ShakedDanZilberman/Magdad/yolo/dataset/test/images/WIN_20250122_15_49_03_Pro_jpg.rf.846b7e2bad95659f3d99197f02cc243a.jpg

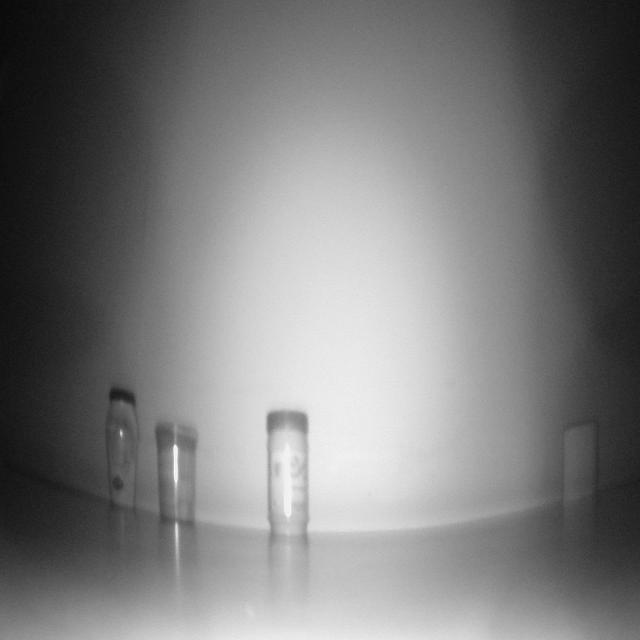
yolo/dataset/test/images/WIN_20250122_15_49_03_Pro_jpg.rf.846b7e2bad95659f3d99197f02cc243a.jpg
