ShakedDanZilberman/Magdad/camera-training-1/valid/images/Screenshot-2025-01-09-204010_jpg.rf.81b5915cf226393bbc3c557325b8a174.jpg

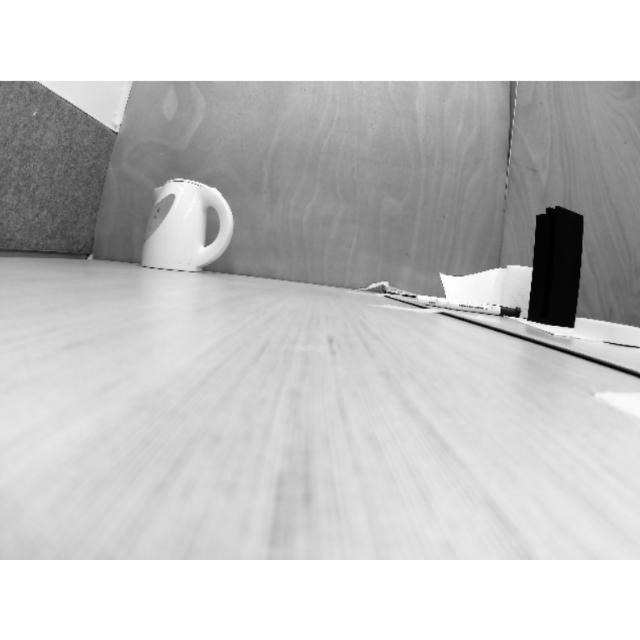
camera-training-1/valid/images/Screenshot-2025-01-09-204010_jpg.rf.81b5915cf226393bbc3c557325b8a174.jpg
