ShakedDanZilberman/Magdad/camera-training-1/valid/images/Screenshot-2025-01-09-204149_jpg.rf.caab2a580253b0b938889a33d17098a2.jpg

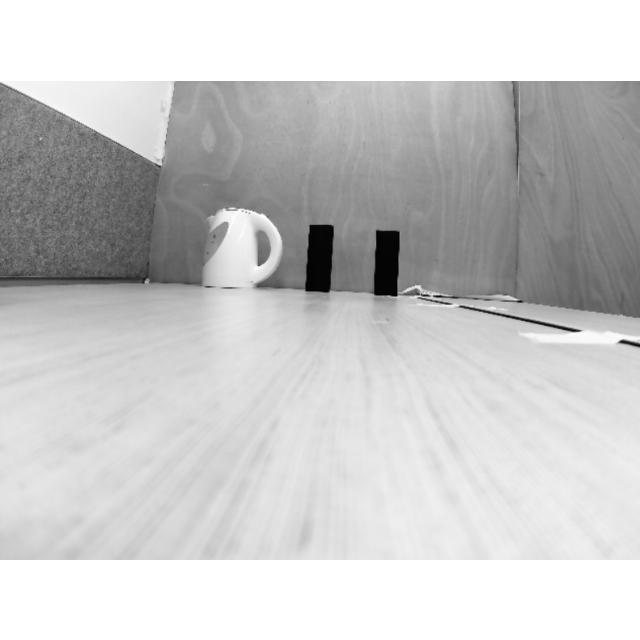
camera-training-1/valid/images/Screenshot-2025-01-09-204149_jpg.rf.caab2a580253b0b938889a33d17098a2.jpg
