ShakedDanZilberman/Magdad/camera-training-1/valid/images/Screenshot-2025-01-09-204222_jpg.rf.880aa902dc17edb48ca99602dae9c156.jpg

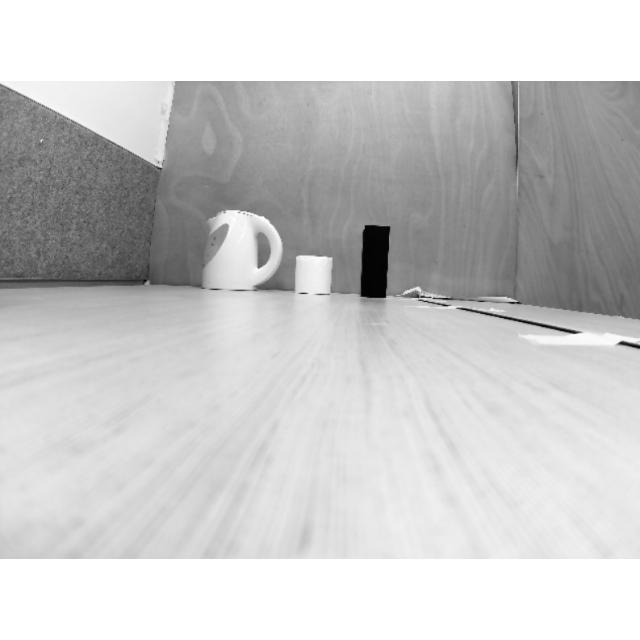
camera-training-1/valid/images/Screenshot-2025-01-09-204222_jpg.rf.880aa902dc17edb48ca99602dae9c156.jpg
