ShakedDanZilberman/Magdad/camera-training-1/valid/images/Screenshot-2025-01-09-204408_jpg.rf.71805534d5d2c8054f3e4067cf0431f8.jpg

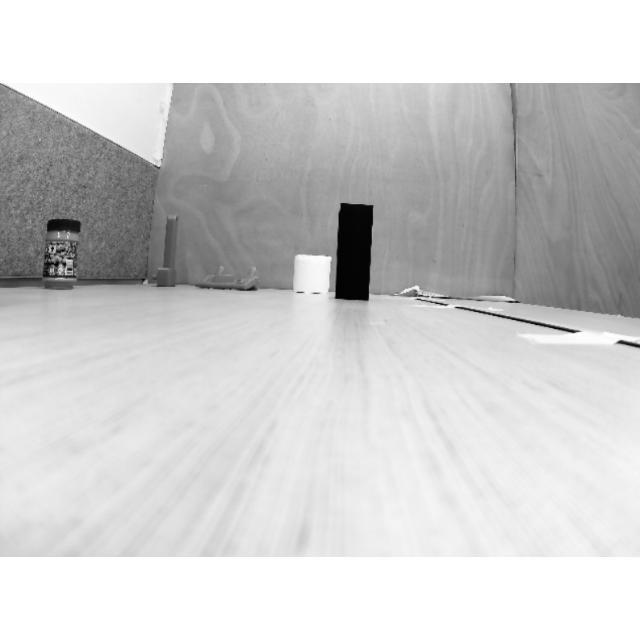
camera-training-1/valid/images/Screenshot-2025-01-09-204408_jpg.rf.71805534d5d2c8054f3e4067cf0431f8.jpg
