ShakedDanZilberman/Magdad/camera-training-1/valid/images/Screenshot-2025-01-09-204434_jpg.rf.ee736907abe9e383c5cfcaa76f32814a.jpg

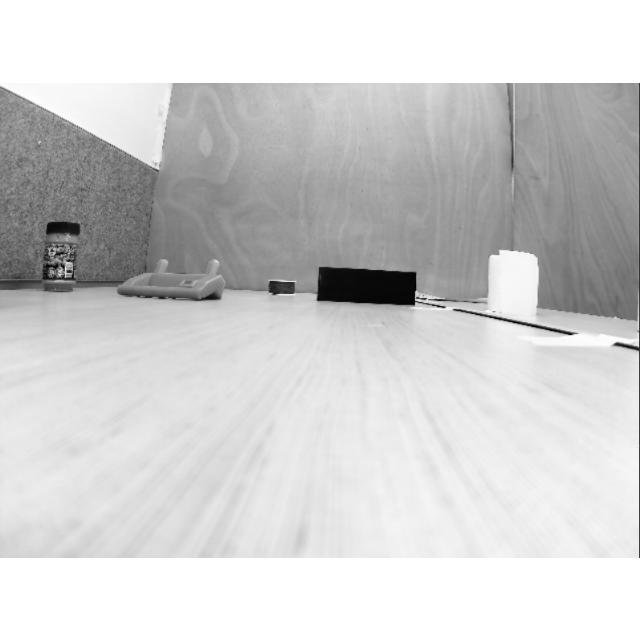
camera-training-1/valid/images/Screenshot-2025-01-09-204434_jpg.rf.ee736907abe9e383c5cfcaa76f32814a.jpg
