ShakedDanZilberman/Magdad/camera-training-1/valid/images/Screenshot-2025-01-09-204518_jpg.rf.a492691f899624e1c3656ebf20315830.jpg

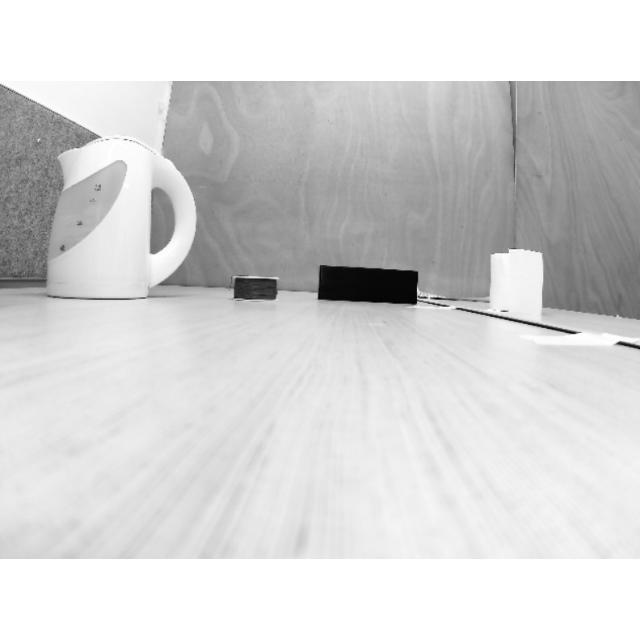
camera-training-1/valid/images/Screenshot-2025-01-09-204518_jpg.rf.a492691f899624e1c3656ebf20315830.jpg
