ShakedDanZilberman/Magdad/camera-training-2/train/images/WIN_20250113_22_33_18_Pro_jpg.rf.e2d5ad69d18867120f0af434011adf48.jpg

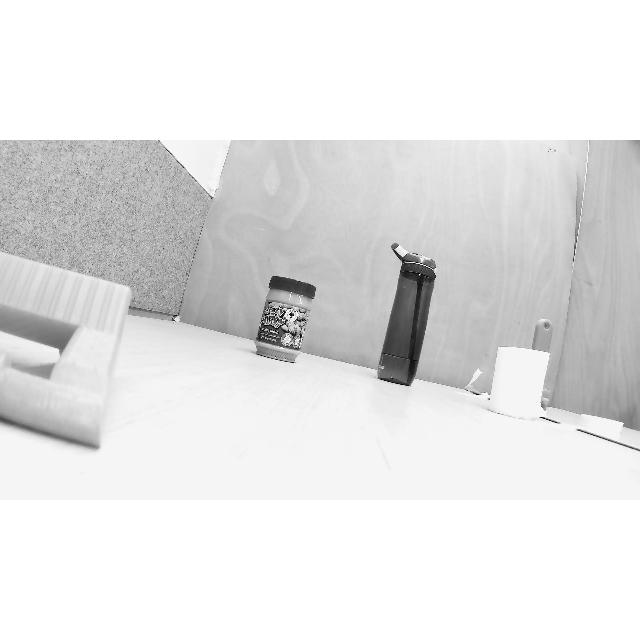
camera-training-2/train/images/WIN_20250113_22_33_18_Pro_jpg.rf.e2d5ad69d18867120f0af434011adf48.jpg
