ShakedDanZilberman/Magdad/camera-training-2/train/images/WIN_20250113_22_33_43_Pro_jpg.rf.7a9c28b805c44db4745cd09ba6515cde.jpg

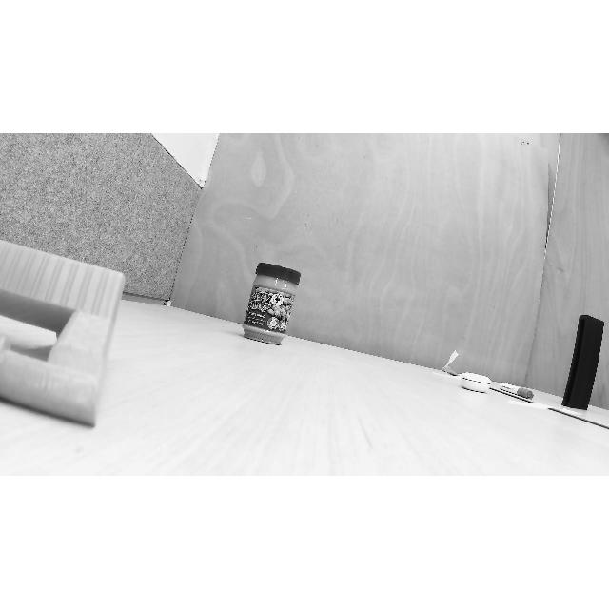
camera-training-2/train/images/WIN_20250113_22_33_43_Pro_jpg.rf.7a9c28b805c44db4745cd09ba6515cde.jpg
