ShakedDanZilberman/Magdad/camera-training-2/train/images/WIN_20250113_22_34_02_Pro_jpg.rf.783c1f57d91c2b72b632802cee9630df.jpg

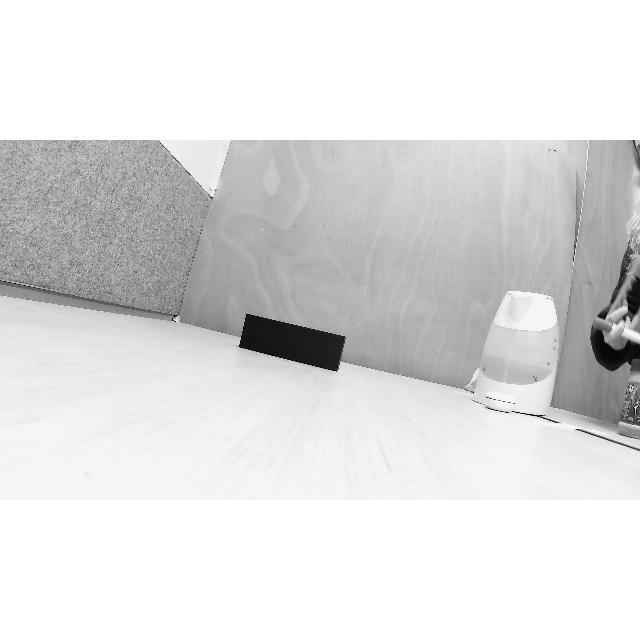
camera-training-2/train/images/WIN_20250113_22_34_02_Pro_jpg.rf.783c1f57d91c2b72b632802cee9630df.jpg
