ShakedDanZilberman/Magdad/camera-training-2/train/images/WIN_20250113_22_34_42_Pro_jpg.rf.ab0f6944b360db3d50f486841ce7cbbd.jpg

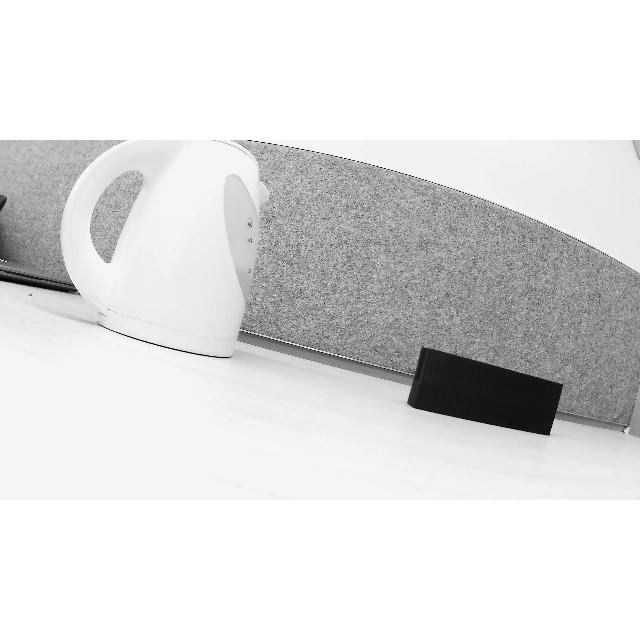
camera-training-2/train/images/WIN_20250113_22_34_42_Pro_jpg.rf.ab0f6944b360db3d50f486841ce7cbbd.jpg
