ShakedDanZilberman/Magdad/camera-training-2/train/images/WIN_20250113_22_34_53_Pro_jpg.rf.5d67e8cbfae78bd698f9c18f5c3b9999.jpg

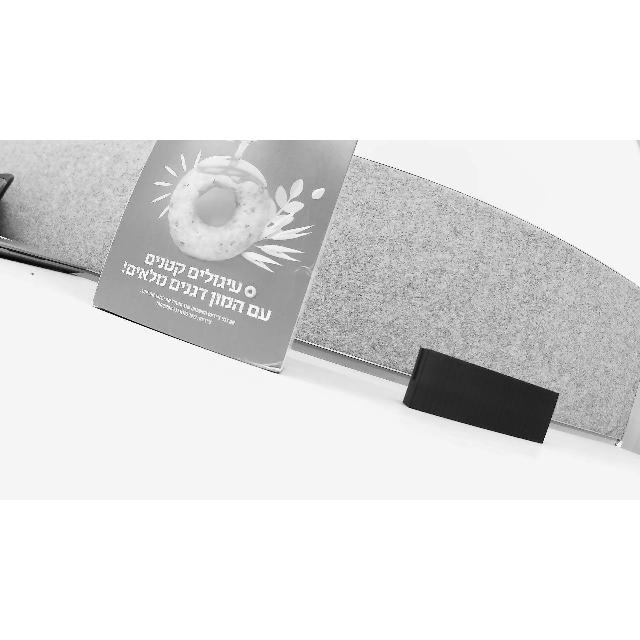
camera-training-2/train/images/WIN_20250113_22_34_53_Pro_jpg.rf.5d67e8cbfae78bd698f9c18f5c3b9999.jpg
