ShakedDanZilberman/Magdad/camera-training-2/train/images/WIN_20250113_22_35_08_Pro_jpg.rf.ca820dc60fe7edaa0e6810bf6f3705b2.jpg

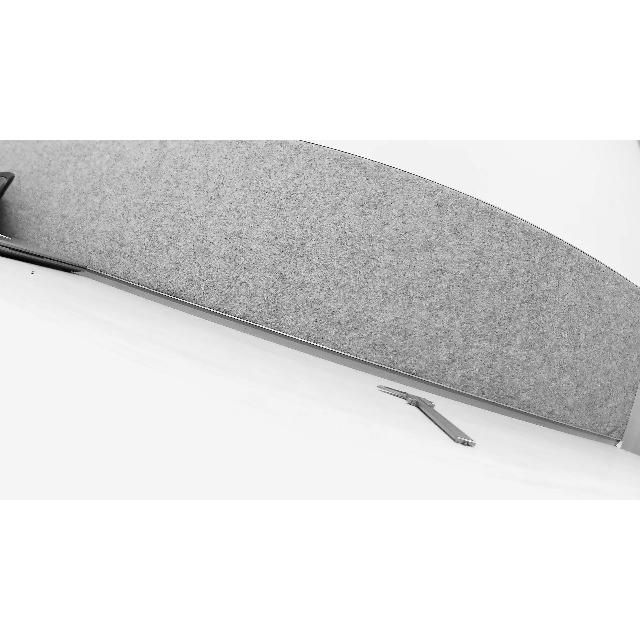
camera-training-2/train/images/WIN_20250113_22_35_08_Pro_jpg.rf.ca820dc60fe7edaa0e6810bf6f3705b2.jpg
