ShakedDanZilberman/Magdad/camera-training-2/train/images/WIN_20250113_22_35_11_Pro_jpg.rf.4013db7eb432c82a8826c612f844e487.jpg

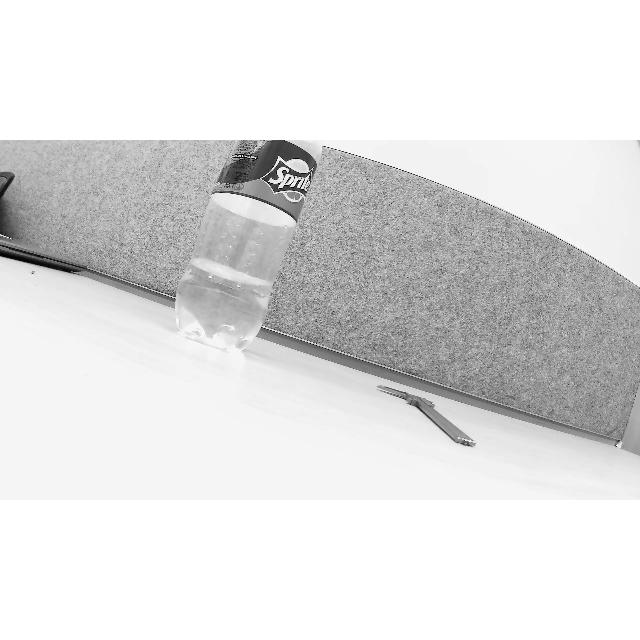
camera-training-2/train/images/WIN_20250113_22_35_11_Pro_jpg.rf.4013db7eb432c82a8826c612f844e487.jpg
