ShakedDanZilberman/Magdad/camera-training-2/train/images/WIN_20250113_22_35_16_Pro_jpg.rf.52b17507b7d4b6b88c684b167f2d8827.jpg

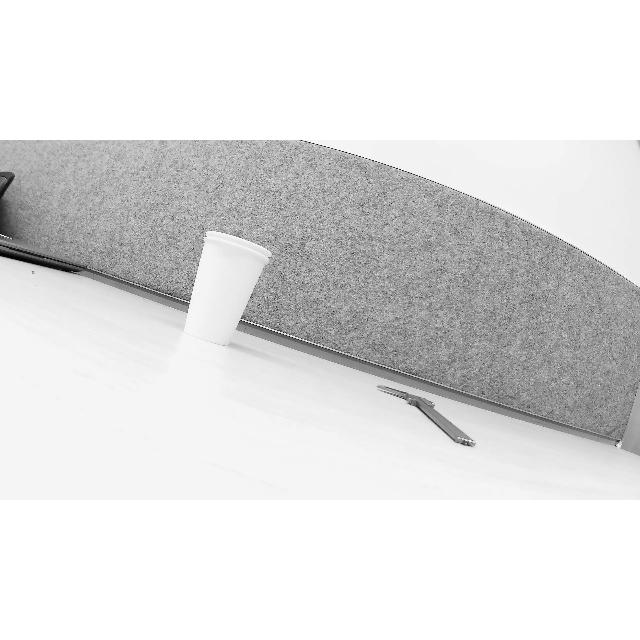
camera-training-2/train/images/WIN_20250113_22_35_16_Pro_jpg.rf.52b17507b7d4b6b88c684b167f2d8827.jpg
