ShakedDanZilberman/Magdad/camera-training-2/train/images/WIN_20250113_22_35_22_Pro_jpg.rf.d8e230dd37e21a51529a2eac11b03157.jpg

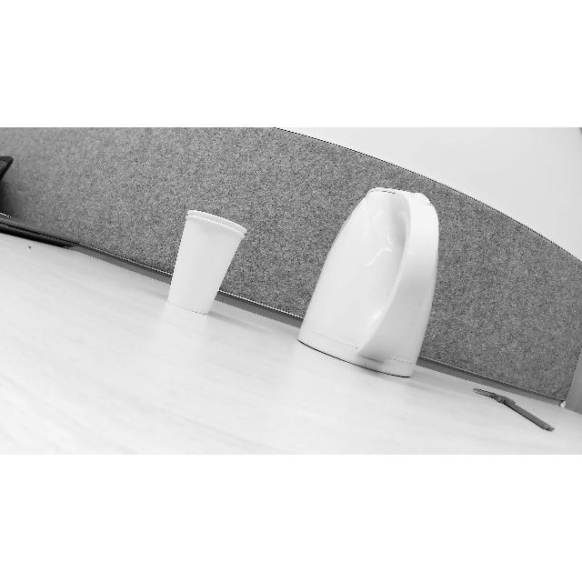
camera-training-2/train/images/WIN_20250113_22_35_22_Pro_jpg.rf.d8e230dd37e21a51529a2eac11b03157.jpg
