ShakedDanZilberman/Magdad/camera-training-2/train/images/WIN_20250113_22_36_17_Pro_jpg.rf.434e08e763b4095fee1812178f245678.jpg

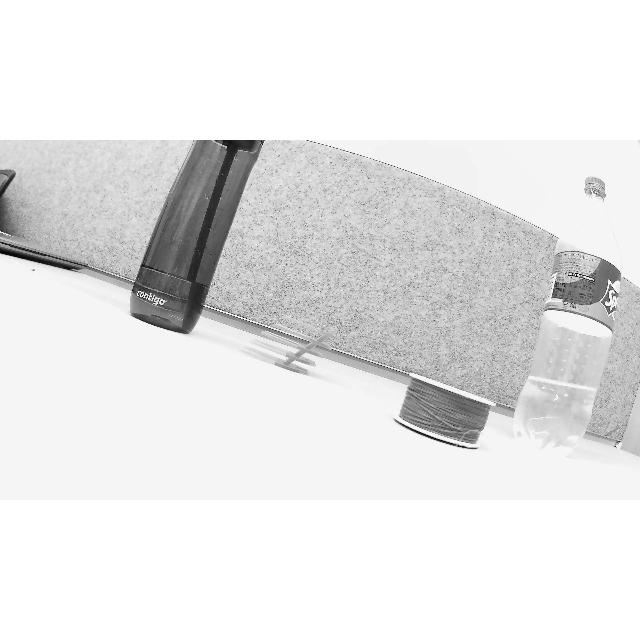
camera-training-2/train/images/WIN_20250113_22_36_17_Pro_jpg.rf.434e08e763b4095fee1812178f245678.jpg
