ShakedDanZilberman/Magdad/camera-training-2/train/images/WIN_20250113_22_37_04_Pro_jpg.rf.e61e84cb694f8d44666576b0f4bd507f.jpg

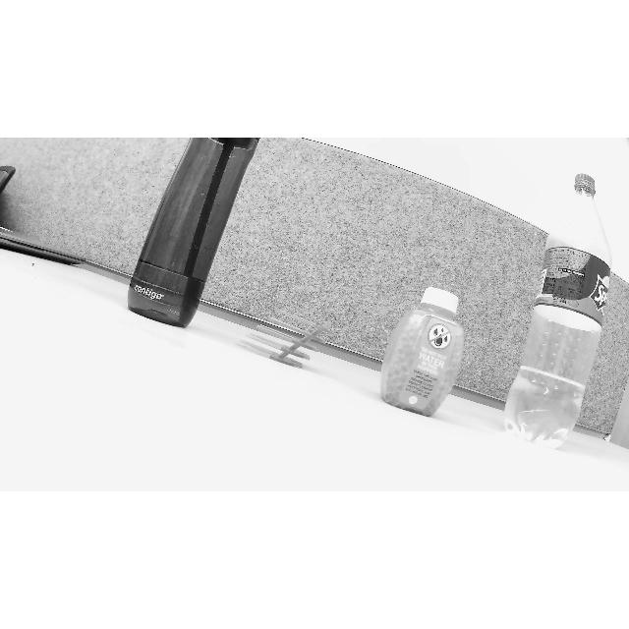
camera-training-2/train/images/WIN_20250113_22_37_04_Pro_jpg.rf.e61e84cb694f8d44666576b0f4bd507f.jpg
