ShakedDanZilberman/Magdad/camera-training-2/train/images/WIN_20250113_22_37_08_Pro_jpg.rf.a589353bd3baeb06a9639a7202b36bbc.jpg

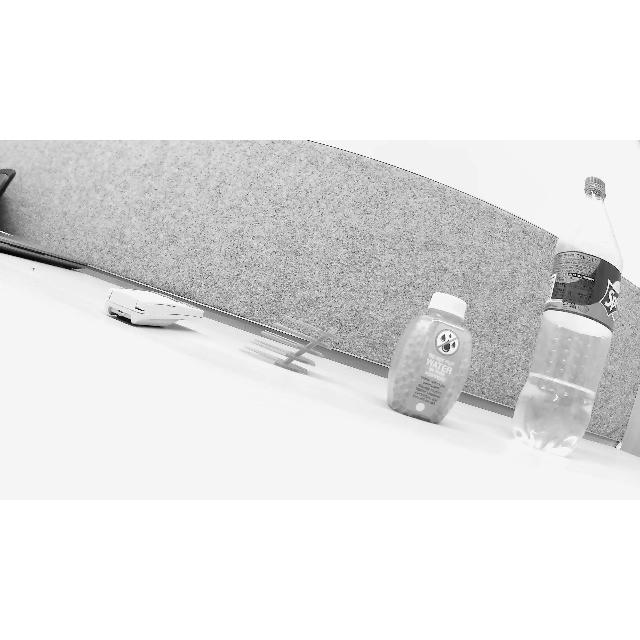
camera-training-2/train/images/WIN_20250113_22_37_08_Pro_jpg.rf.a589353bd3baeb06a9639a7202b36bbc.jpg
