ShakedDanZilberman/Magdad/camera-training-2/train/images/WIN_20250113_22_37_36_Pro_jpg.rf.b33690e6ef2aee6fb451731b02019a81.jpg

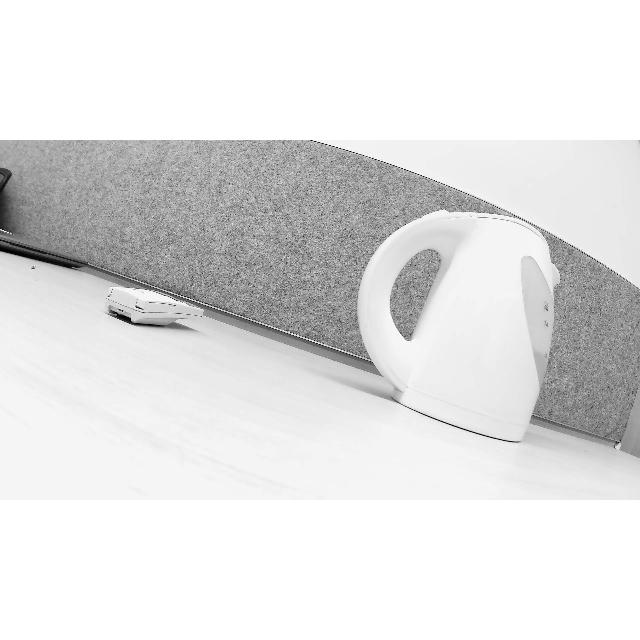
camera-training-2/train/images/WIN_20250113_22_37_36_Pro_jpg.rf.b33690e6ef2aee6fb451731b02019a81.jpg
