ShakedDanZilberman/Magdad/camera-training-2/train/images/WIN_20250113_22_37_51_Pro_jpg.rf.b9c5b7d6a7c29c52d90a4989442c4607.jpg

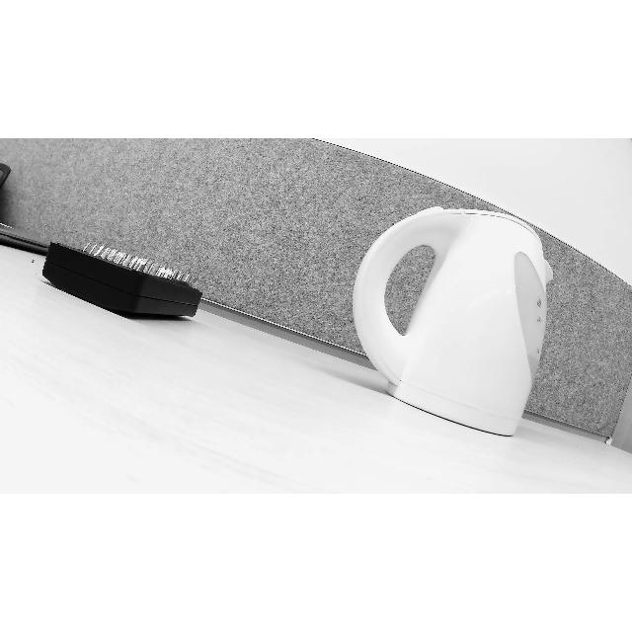
camera-training-2/train/images/WIN_20250113_22_37_51_Pro_jpg.rf.b9c5b7d6a7c29c52d90a4989442c4607.jpg
