ShakedDanZilberman/Magdad/camera-training-2/train/images/WIN_20250113_22_38_17_Pro_jpg.rf.8e4c9293f9f154b4c6c96e188bc1d038.jpg

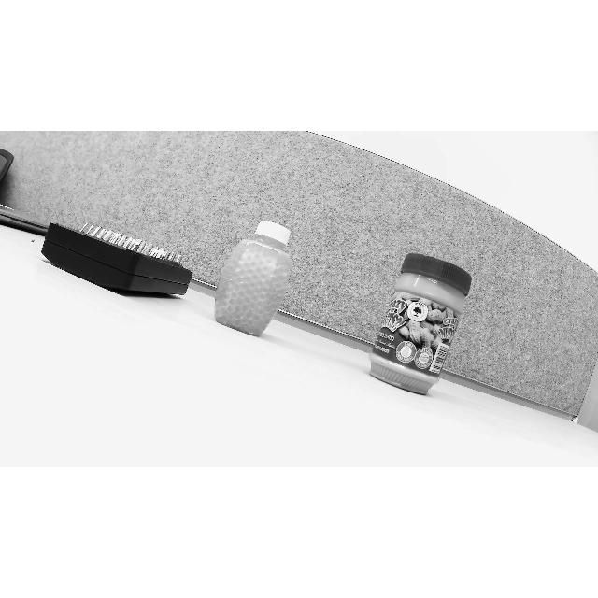
camera-training-2/train/images/WIN_20250113_22_38_17_Pro_jpg.rf.8e4c9293f9f154b4c6c96e188bc1d038.jpg
