ShakedDanZilberman/Magdad/camera-training-2/train/images/WIN_20250113_22_38_23_Pro_jpg.rf.5dbb93d275ae0dcbff493e2a2543c315.jpg

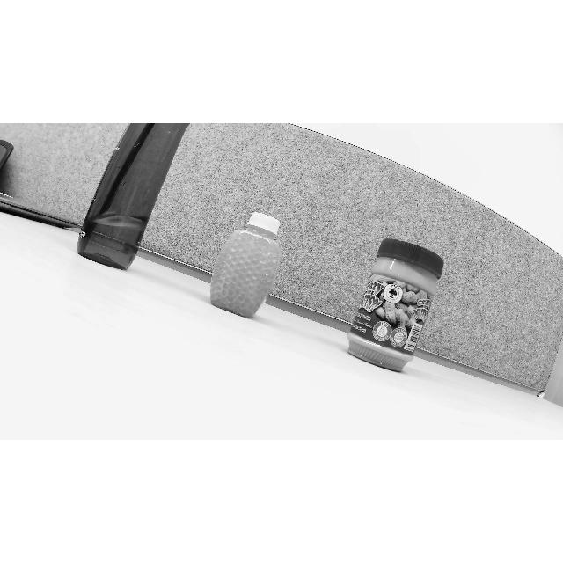
camera-training-2/train/images/WIN_20250113_22_38_23_Pro_jpg.rf.5dbb93d275ae0dcbff493e2a2543c315.jpg
