ShakedDanZilberman/Magdad/camera-training-2/train/images/WIN_20250113_22_38_47_Pro_jpg.rf.66622b3fdd767c53d6206cc575598a07.jpg

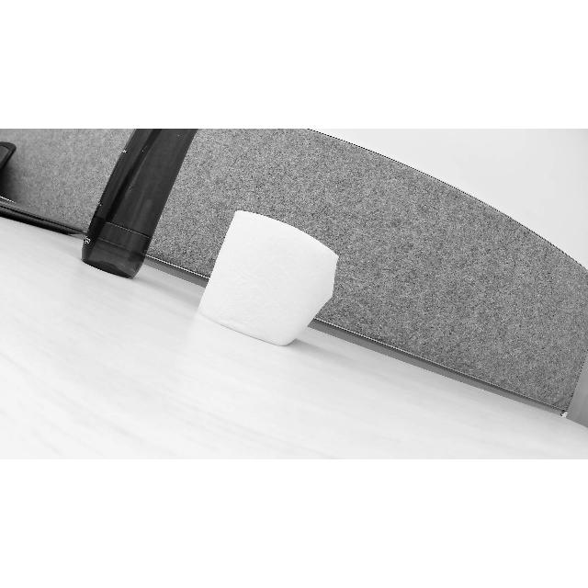
camera-training-2/train/images/WIN_20250113_22_38_47_Pro_jpg.rf.66622b3fdd767c53d6206cc575598a07.jpg
