ShakedDanZilberman/Magdad/camera-training-2/train/images/WIN_20250113_22_39_10_Pro_jpg.rf.253a86497d2ba91eef1dbaa0058f9085.jpg

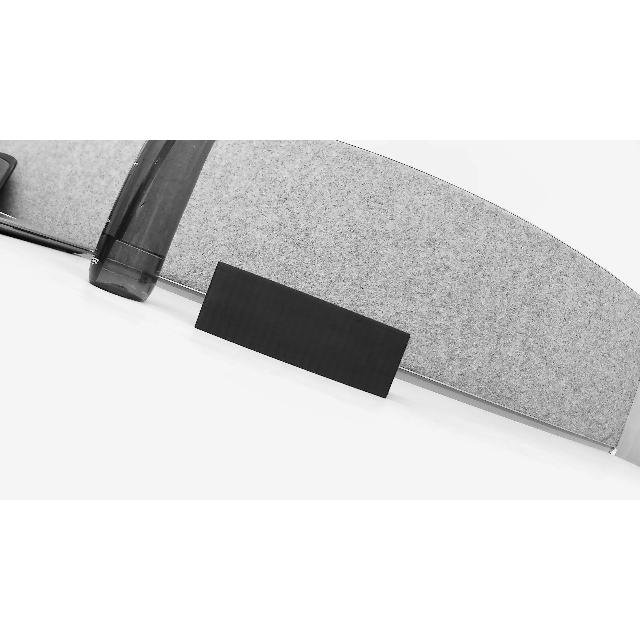
camera-training-2/train/images/WIN_20250113_22_39_10_Pro_jpg.rf.253a86497d2ba91eef1dbaa0058f9085.jpg
