ShakedDanZilberman/Magdad/camera-training-2/train/images/WIN_20250113_22_39_30_Pro_jpg.rf.a8221e1a47ee683b0f74e122a8c80f67.jpg

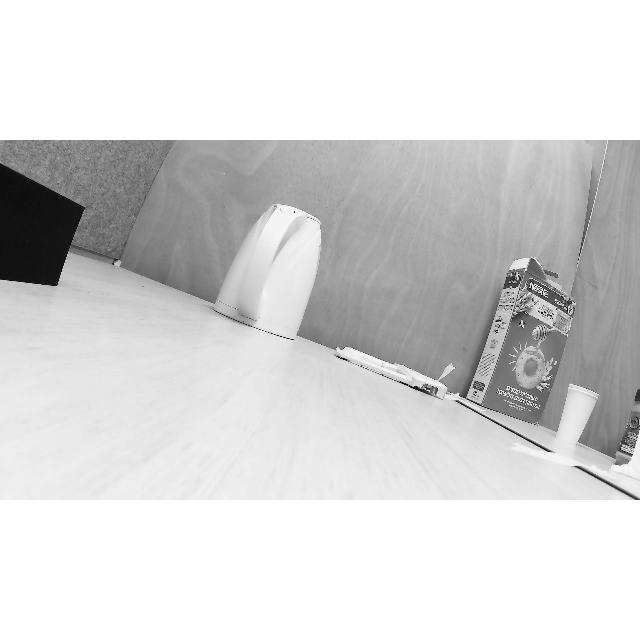
camera-training-2/train/images/WIN_20250113_22_39_30_Pro_jpg.rf.a8221e1a47ee683b0f74e122a8c80f67.jpg
