ShakedDanZilberman/Magdad/camera-training-2/train/images/WIN_20250113_22_39_38_Pro_jpg.rf.3bc607d0f519e104844494635457f564.jpg

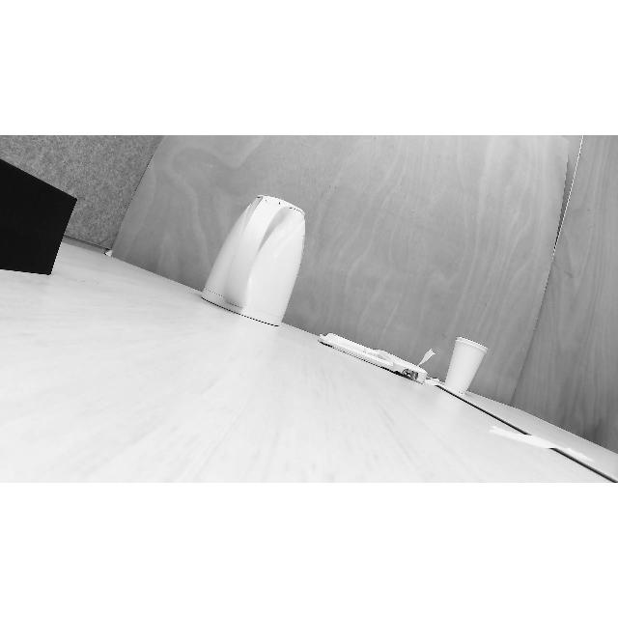
camera-training-2/train/images/WIN_20250113_22_39_38_Pro_jpg.rf.3bc607d0f519e104844494635457f564.jpg
