ShakedDanZilberman/Magdad/camera-training-2/train/images/WIN_20250113_22_40_06_Pro_jpg.rf.6f355db6460bb0738abd5323291e1bff.jpg

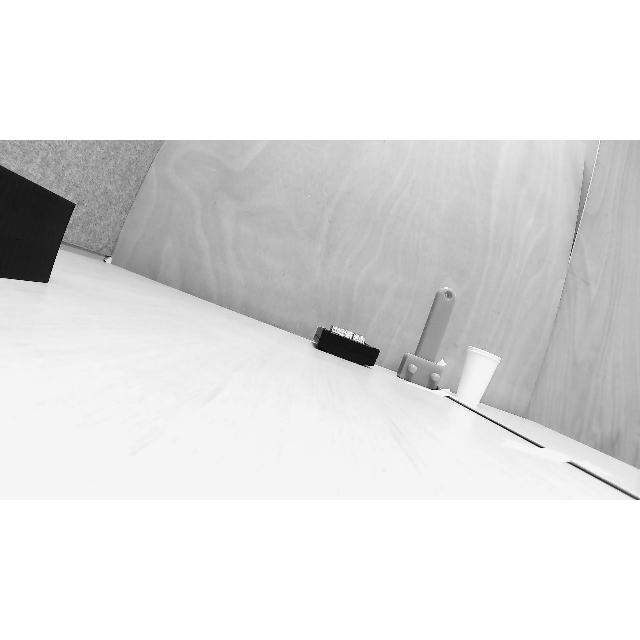
camera-training-2/train/images/WIN_20250113_22_40_06_Pro_jpg.rf.6f355db6460bb0738abd5323291e1bff.jpg
