ShakedDanZilberman/Magdad/camera-training-2/train/images/WIN_20250113_22_40_22_Pro_jpg.rf.743f60de3c918ec63ab65db9a79bd959.jpg

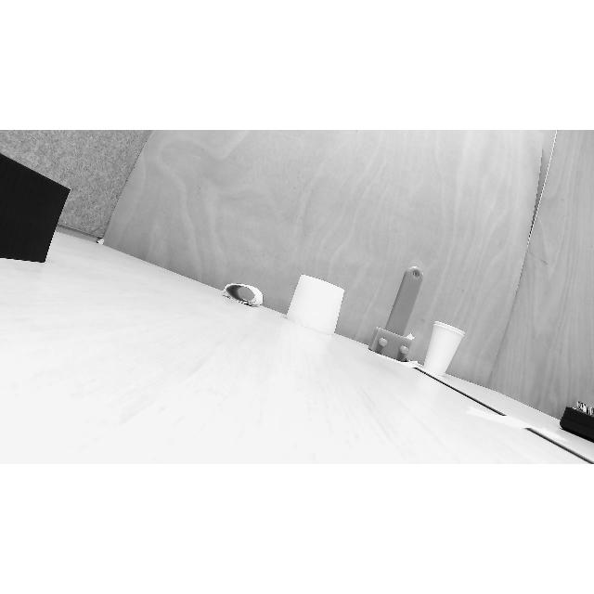
camera-training-2/train/images/WIN_20250113_22_40_22_Pro_jpg.rf.743f60de3c918ec63ab65db9a79bd959.jpg
