ShakedDanZilberman/Magdad/camera-training-2/train/images/WIN_20250113_22_41_05_Pro_jpg.rf.81757d52d88d5fbfa62f40eb433f8090.jpg

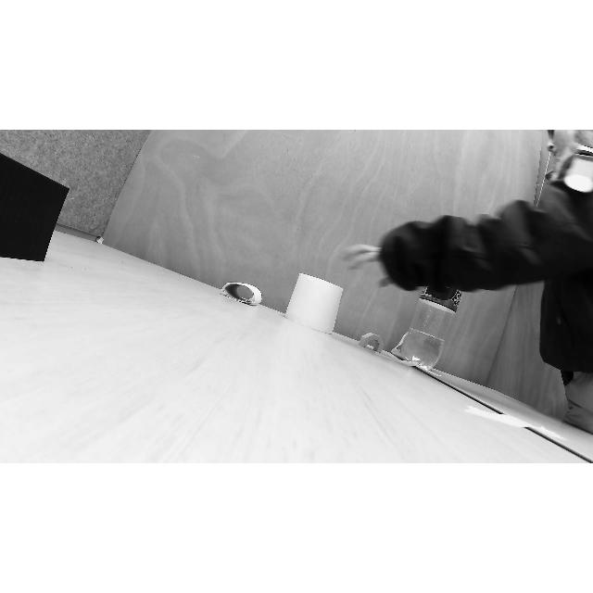
camera-training-2/train/images/WIN_20250113_22_41_05_Pro_jpg.rf.81757d52d88d5fbfa62f40eb433f8090.jpg
