ShakedDanZilberman/Magdad/camera-training-2/train/images/WIN_20250113_22_42_10_Pro_jpg.rf.32e12ff022c67c932389b7111940035a.jpg

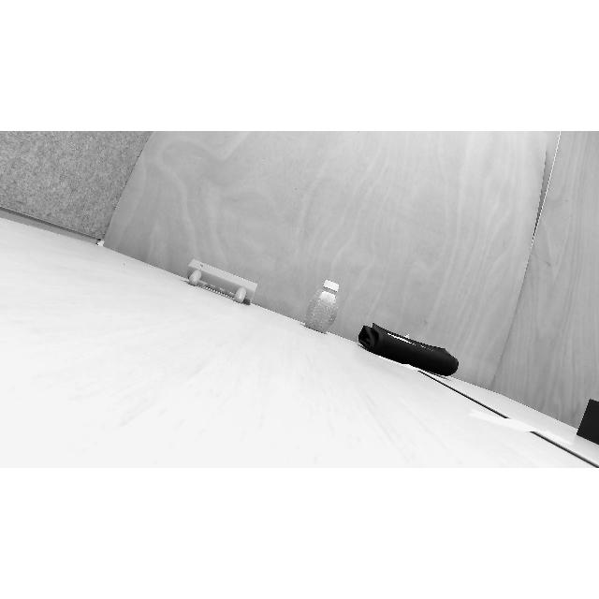
camera-training-2/train/images/WIN_20250113_22_42_10_Pro_jpg.rf.32e12ff022c67c932389b7111940035a.jpg
