ShakedDanZilberman/Magdad/camera-training-2/train/images/WIN_20250113_22_42_40_Pro_jpg.rf.92384597ecd3b0a4bffcabb38320616e.jpg

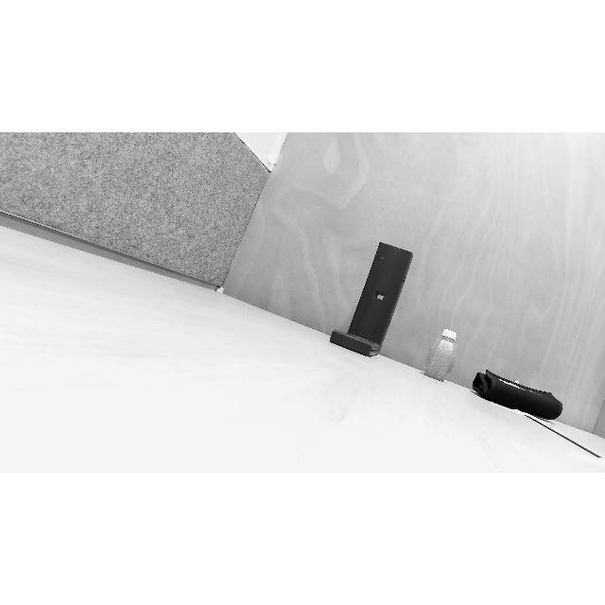
camera-training-2/train/images/WIN_20250113_22_42_40_Pro_jpg.rf.92384597ecd3b0a4bffcabb38320616e.jpg
