ShakedDanZilberman/Magdad/camera-training-2/train/images/WIN_20250113_22_42_48_Pro_jpg.rf.e93ffbc472efff108b7a3c59b1170274.jpg

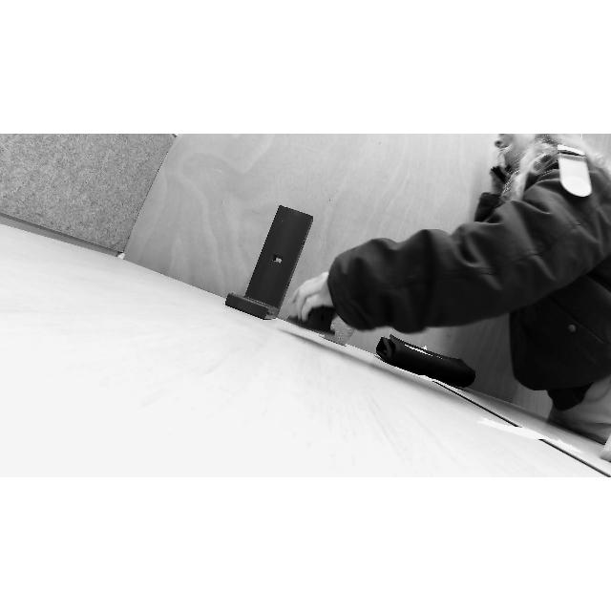
camera-training-2/train/images/WIN_20250113_22_42_48_Pro_jpg.rf.e93ffbc472efff108b7a3c59b1170274.jpg
