ShakedDanZilberman/Magdad/camera-training-2/train/images/WIN_20250113_22_43_01_Pro_jpg.rf.85477816b50bfda8253a108ba01e3208.jpg

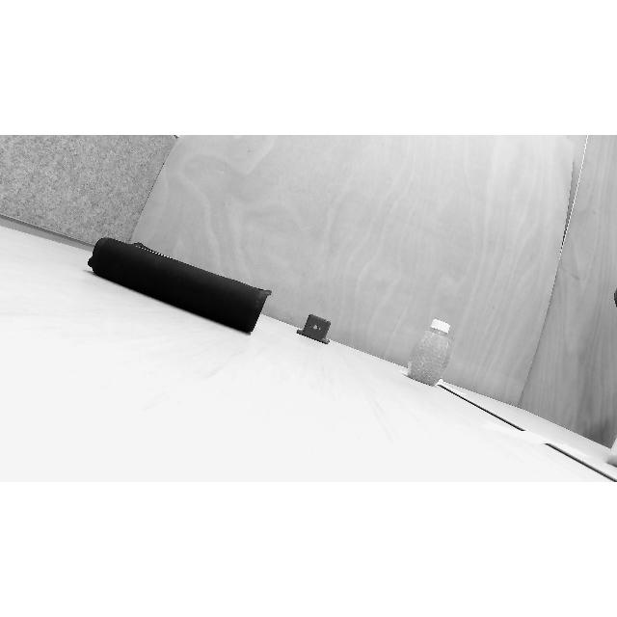
camera-training-2/train/images/WIN_20250113_22_43_01_Pro_jpg.rf.85477816b50bfda8253a108ba01e3208.jpg
