ShakedDanZilberman/Magdad/camera-training-2/train/images/WIN_20250113_22_43_12_Pro_jpg.rf.de70a53ec0a42eb00e3af8e9a14324cf.jpg

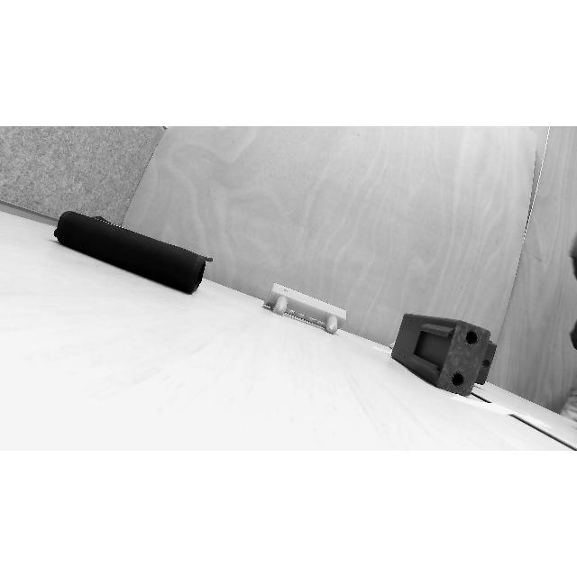
camera-training-2/train/images/WIN_20250113_22_43_12_Pro_jpg.rf.de70a53ec0a42eb00e3af8e9a14324cf.jpg
