ShakedDanZilberman/Magdad/camera-training-2/train/images/WIN_20250113_22_43_33_Pro_jpg.rf.30e844897ff9256df4f26eb0bfbda52d.jpg

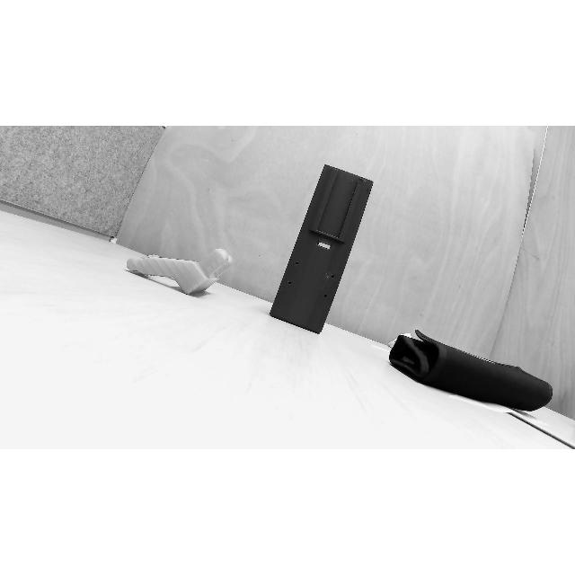
camera-training-2/train/images/WIN_20250113_22_43_33_Pro_jpg.rf.30e844897ff9256df4f26eb0bfbda52d.jpg
