ShakedDanZilberman/Magdad/camera-training-2/train/images/WIN_20250113_22_44_00_Pro_jpg.rf.20149d039af8cff58ac0f18044d618da.jpg

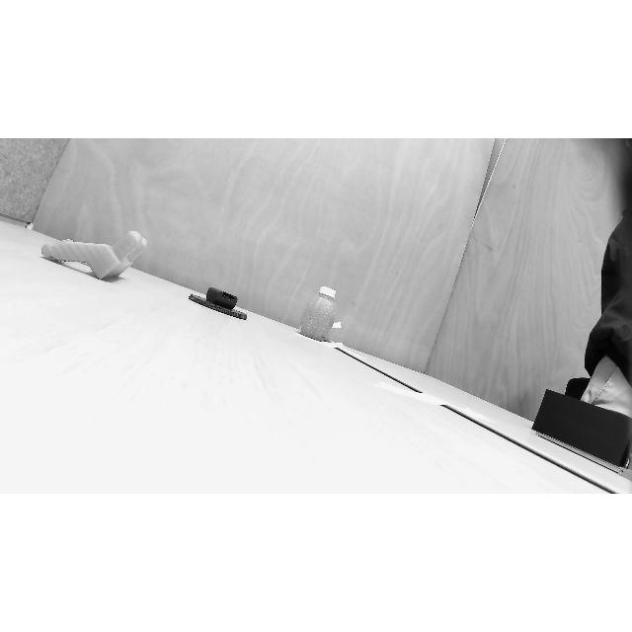
camera-training-2/train/images/WIN_20250113_22_44_00_Pro_jpg.rf.20149d039af8cff58ac0f18044d618da.jpg
