ShakedDanZilberman/Magdad/camera-training-2/train/images/WIN_20250113_22_44_12_Pro_jpg.rf.9b10c28fe63c1ae49be889de22b8d8f4.jpg

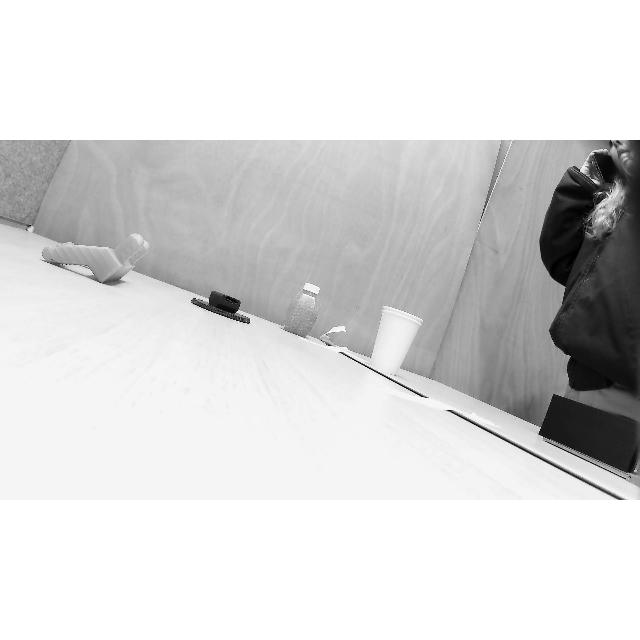
camera-training-2/train/images/WIN_20250113_22_44_12_Pro_jpg.rf.9b10c28fe63c1ae49be889de22b8d8f4.jpg
