ShakedDanZilberman/Magdad/camera-training-2/train/images/WIN_20250113_22_44_56_Pro_jpg.rf.4f9d95a4c188d3bfc7a40898143e7159.jpg

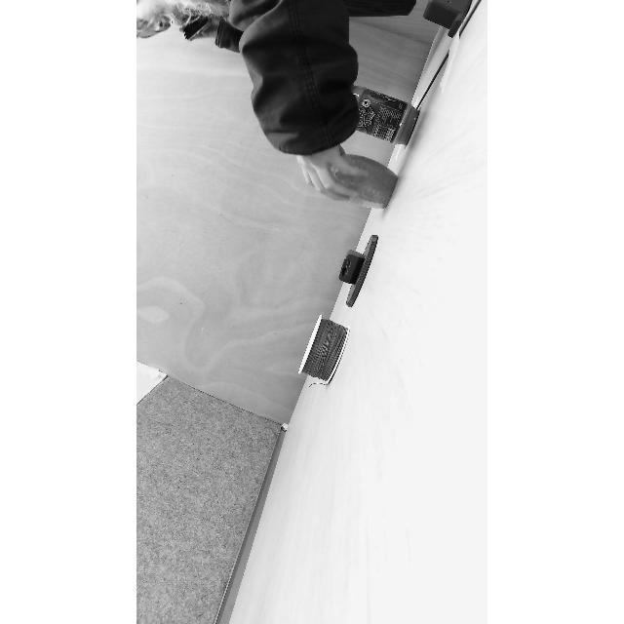
camera-training-2/train/images/WIN_20250113_22_44_56_Pro_jpg.rf.4f9d95a4c188d3bfc7a40898143e7159.jpg
