ShakedDanZilberman/Magdad/camera-training-2/train/images/WIN_20250113_22_44_57_Pro_jpg.rf.8f4678745a50cfe26ac4a26389f38c47.jpg

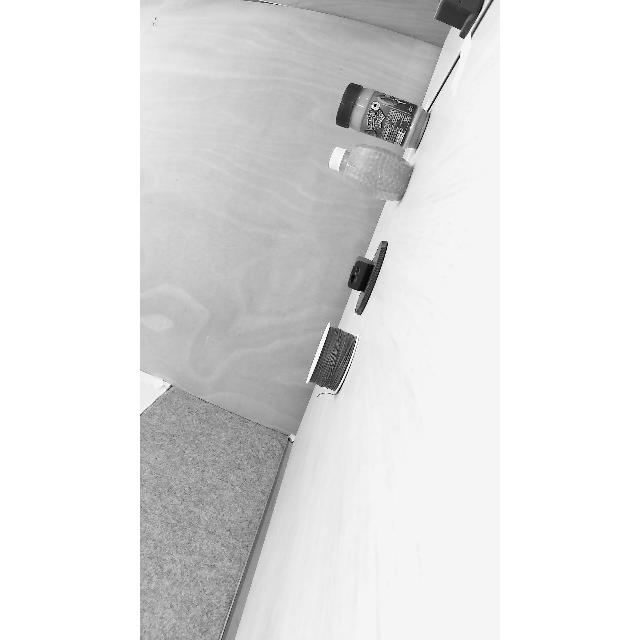
camera-training-2/train/images/WIN_20250113_22_44_57_Pro_jpg.rf.8f4678745a50cfe26ac4a26389f38c47.jpg
