ShakedDanZilberman/Magdad/camera-training-2/train/images/WIN_20250113_22_45_20_Pro_jpg.rf.0e5be70096149867ba9fe1c749a1d6bc.jpg

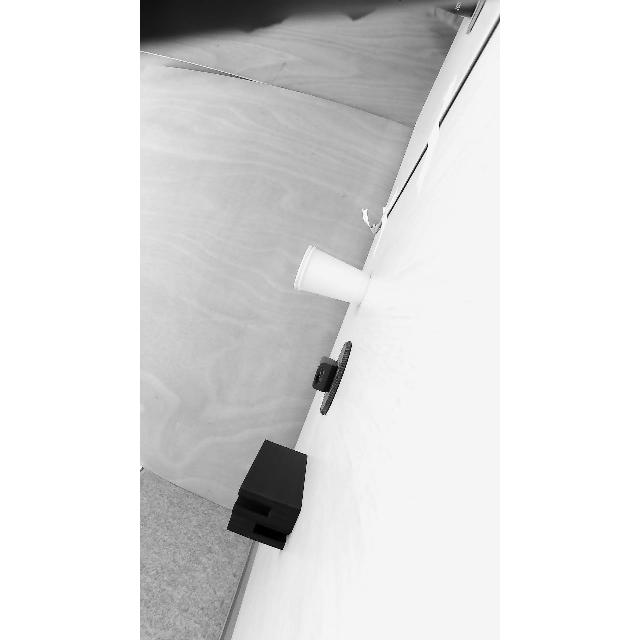
camera-training-2/train/images/WIN_20250113_22_45_20_Pro_jpg.rf.0e5be70096149867ba9fe1c749a1d6bc.jpg
