ShakedDanZilberman/Magdad/camera-training-2/train/images/WIN_20250113_22_45_49_Pro_jpg.rf.75c45d366dac1b87cdeff89ad048964c.jpg

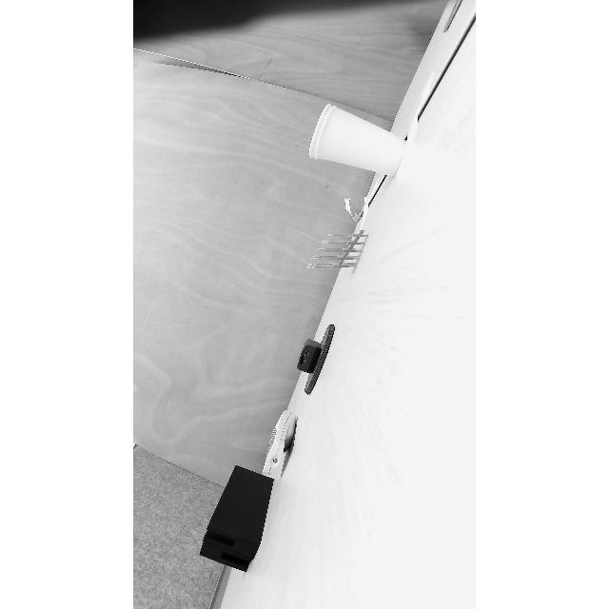
camera-training-2/train/images/WIN_20250113_22_45_49_Pro_jpg.rf.75c45d366dac1b87cdeff89ad048964c.jpg
