ShakedDanZilberman/Magdad/camera-training-2/train/images/WIN_20250113_22_46_08_Pro_jpg.rf.6a4b9376a5a9358eb9978b5d456c83fb.jpg

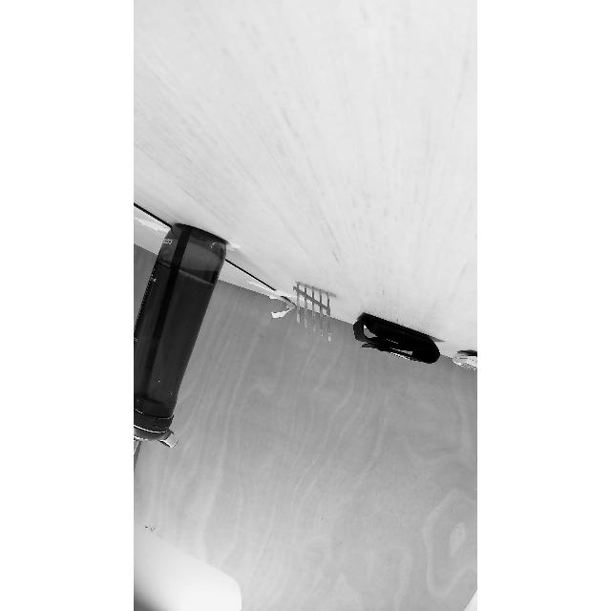
camera-training-2/train/images/WIN_20250113_22_46_08_Pro_jpg.rf.6a4b9376a5a9358eb9978b5d456c83fb.jpg
