ShakedDanZilberman/Magdad/camera-training-2/train/images/WIN_20250113_22_46_31_Pro_jpg.rf.7ee1fa83034b78e504ae16af33be2816.jpg

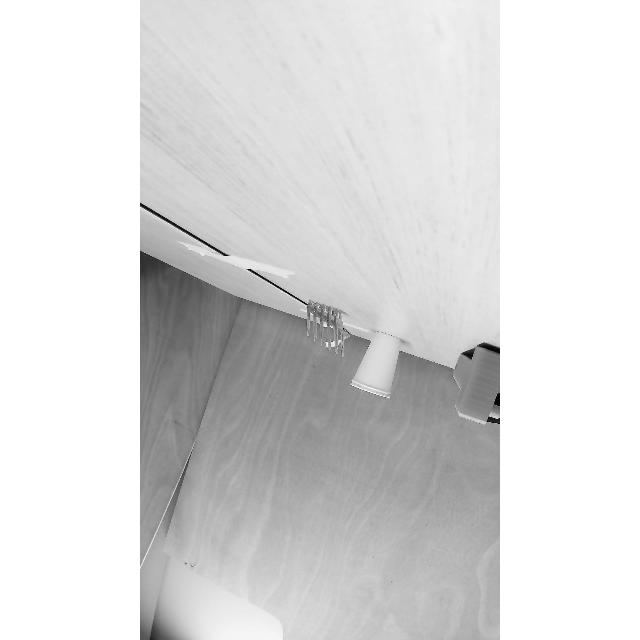
camera-training-2/train/images/WIN_20250113_22_46_31_Pro_jpg.rf.7ee1fa83034b78e504ae16af33be2816.jpg
