ShakedDanZilberman/Magdad/camera-training-2/valid/images/WIN_20250113_22_34_45_Pro_jpg.rf.2d769679200d2a4043b8c2123827f19e.jpg

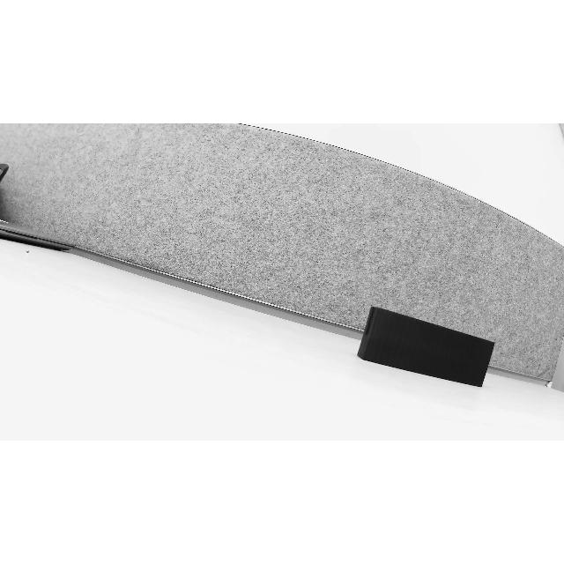
camera-training-2/valid/images/WIN_20250113_22_34_45_Pro_jpg.rf.2d769679200d2a4043b8c2123827f19e.jpg
