ShakedDanZilberman/Magdad/camera-training-2/valid/images/WIN_20250113_22_35_41_Pro_jpg.rf.0fb7a3f226adb98dac5fb6182e68275d.jpg

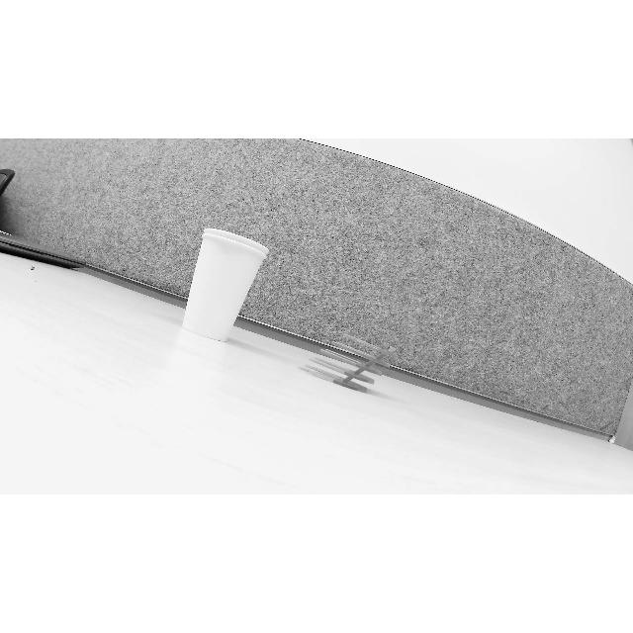
camera-training-2/valid/images/WIN_20250113_22_35_41_Pro_jpg.rf.0fb7a3f226adb98dac5fb6182e68275d.jpg
