ShakedDanZilberman/Magdad/camera-training-2/valid/images/WIN_20250113_22_36_08_Pro_jpg.rf.fee2e06f307be7eaafe471c80bef39ea.jpg

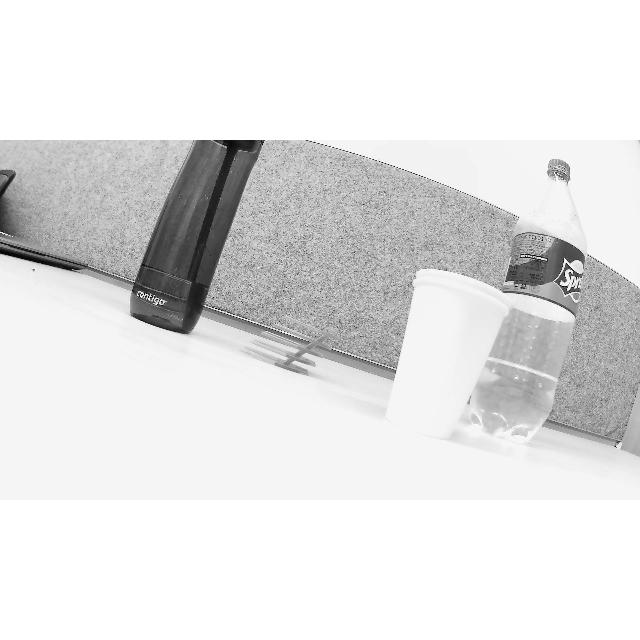
camera-training-2/valid/images/WIN_20250113_22_36_08_Pro_jpg.rf.fee2e06f307be7eaafe471c80bef39ea.jpg
