ShakedDanZilberman/Magdad/homography_pics/WIN_20250407_21_24_59_Pro.jpg

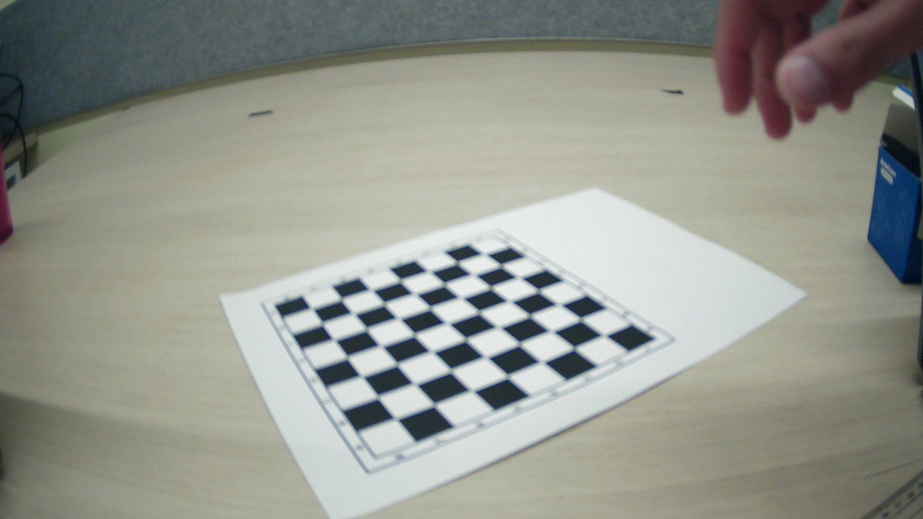
homography_pics/WIN_20250407_21_24_59_Pro.jpg
