ShakedDanZilberman/Magdad/homography_pics/WIN_20250407_21_25_56_Pro.jpg

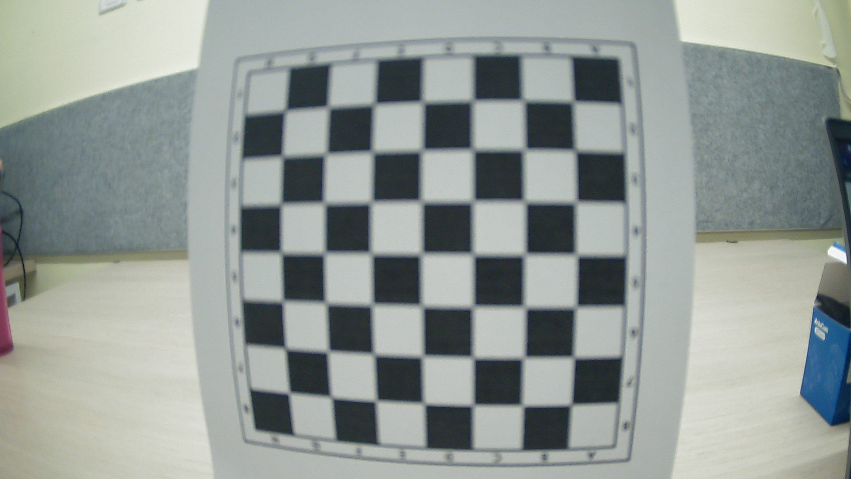
homography_pics/WIN_20250407_21_25_56_Pro.jpg
