ShakedDanZilberman/Magdad/homography_pics/WIN_20250407_21_26_44_Pro.jpg

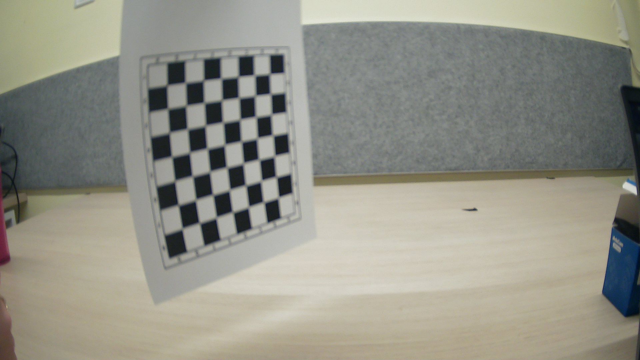
homography_pics/WIN_20250407_21_26_44_Pro.jpg
