ShakedDanZilberman/Magdad/photographic_resources/IR image.jpg

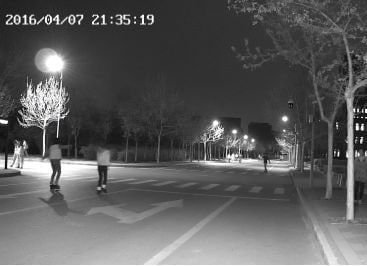
photographic_resources/IR image.jpg
