ShakedDanZilberman/Magdad/WIN_20250105_20_42_05_Pro.jpg

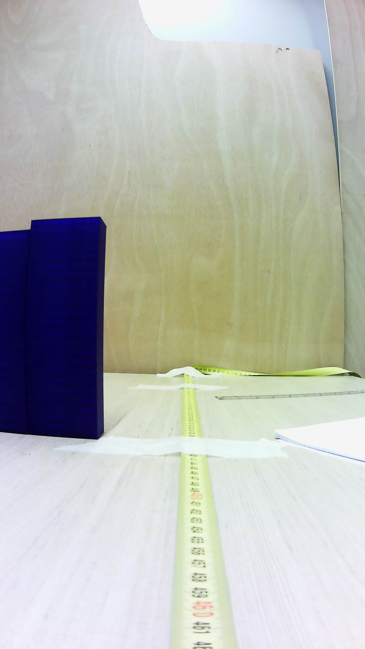
WIN_20250105_20_42_05_Pro.jpg
