ShakedDanZilberman/Magdad/yolo/dataset/valid/images/WIN_20250122_15_54_56_Pro-Copy_jpg.rf.3b5c02901a851303788aae91fb613a67.jpg

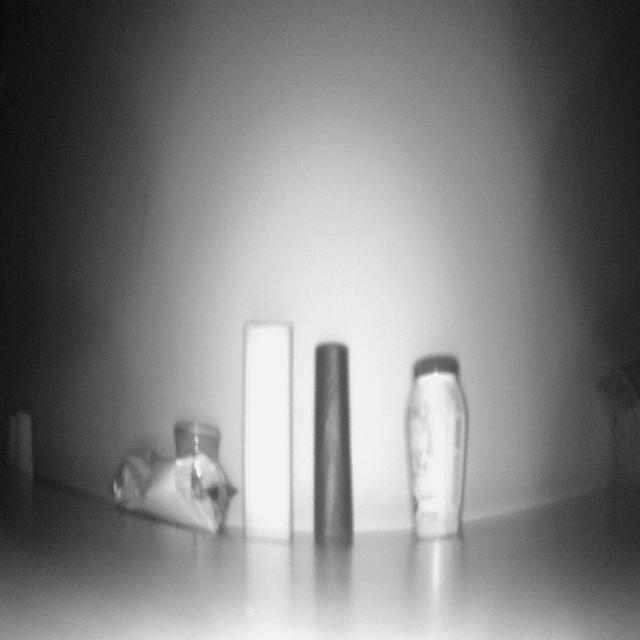
yolo/dataset/valid/images/WIN_20250122_15_54_56_Pro-Copy_jpg.rf.3b5c02901a851303788aae91fb613a67.jpg
