ShakedDanZilberman/Magdad/yolo/dataset/valid/images/WIN_20250122_15_55_26_Pro-Copy_jpg.rf.33c6cb033a6c215a2a4cb4606a892f1c.jpg

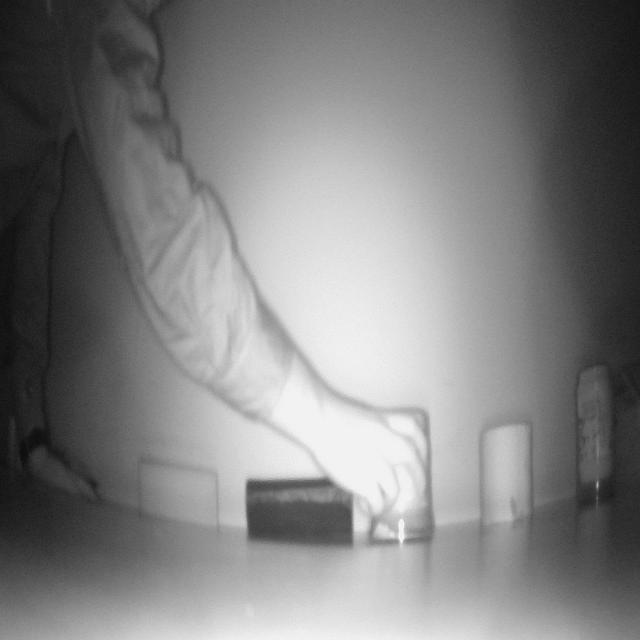
yolo/dataset/valid/images/WIN_20250122_15_55_26_Pro-Copy_jpg.rf.33c6cb033a6c215a2a4cb4606a892f1c.jpg
