ShakedDanZilberman/Magdad/yolo/images/img1.jpg

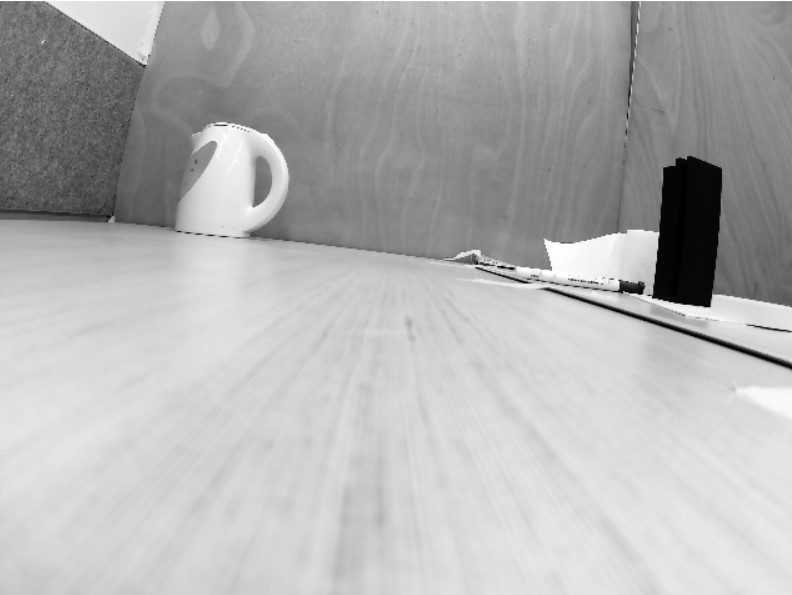
yolo/images/img1.jpg
