ShakedDanZilberman/Magdad/yolo/images/img2.jpg

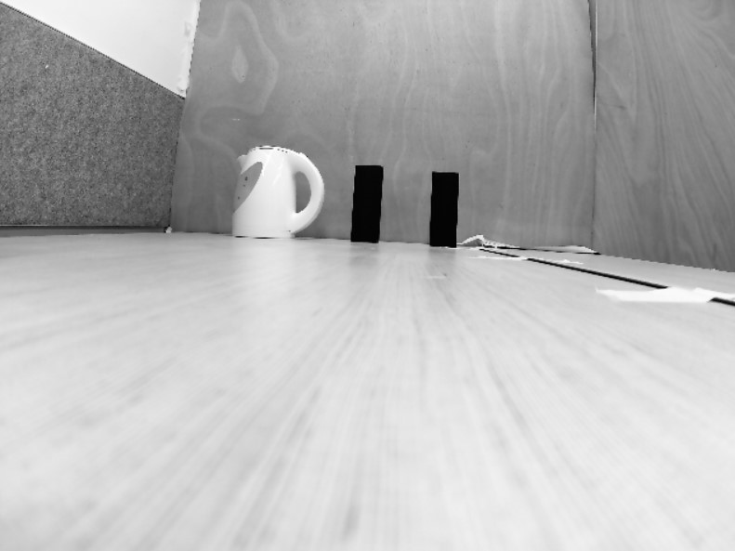
yolo/images/img2.jpg
