ShakedDanZilberman/Magdad/yolo/images/img4.jpg

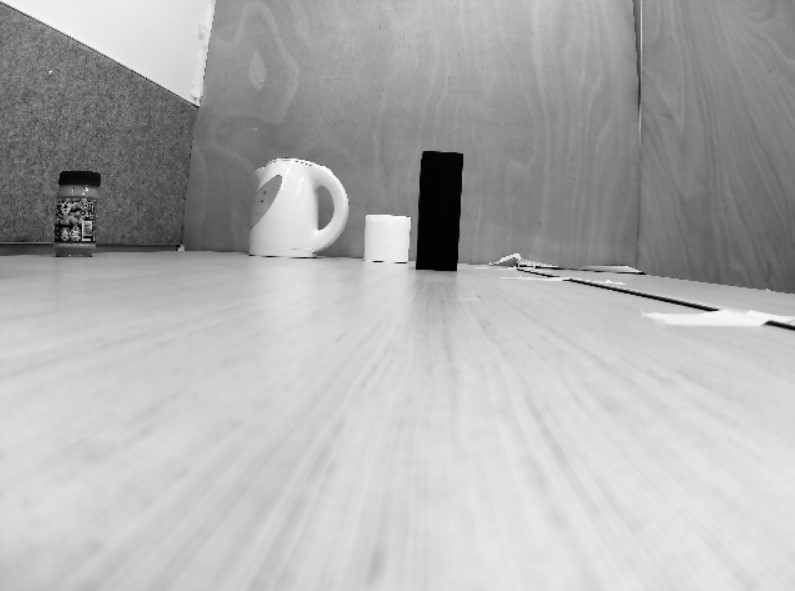
yolo/images/img4.jpg
