ShakedDanZilberman/Magdad/yolo/images/img5.jpg

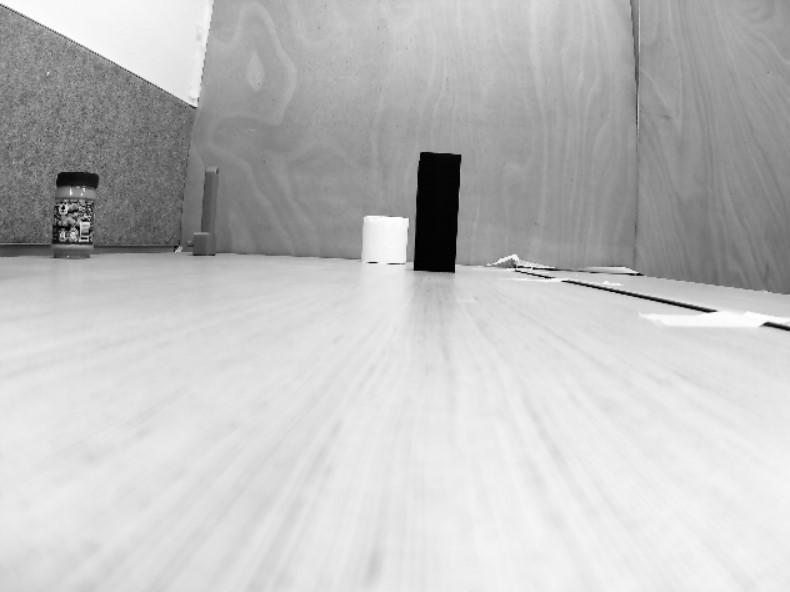
yolo/images/img5.jpg
