ShakedDanZilberman/Magdad/yolo/images/img7.jpg

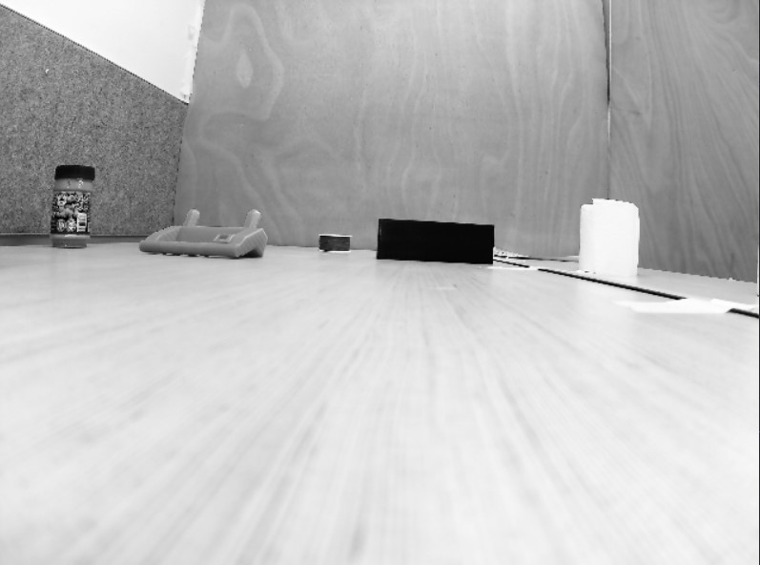
yolo/images/img7.jpg
