ShakedDanZilberman/Magdad/yolo/images/img8.jpg

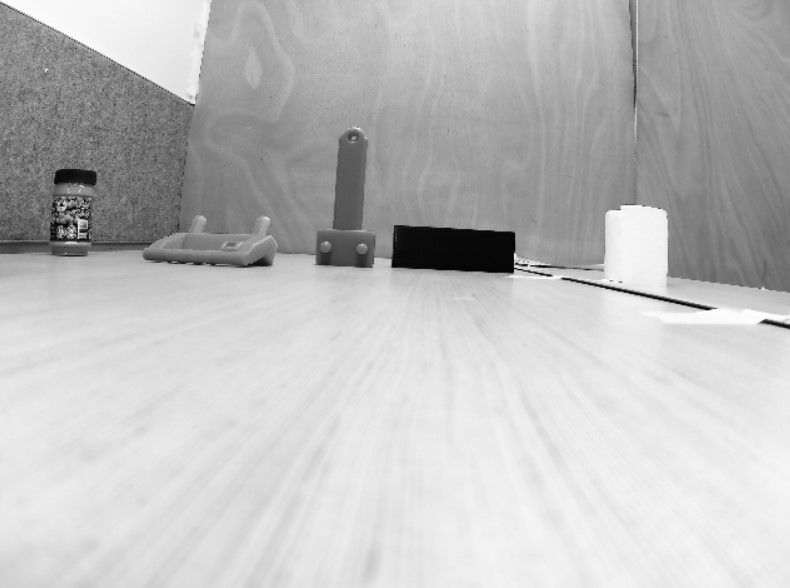
yolo/images/img8.jpg
