ShakedDanZilberman/Magdad/yolo/images/img9.jpg

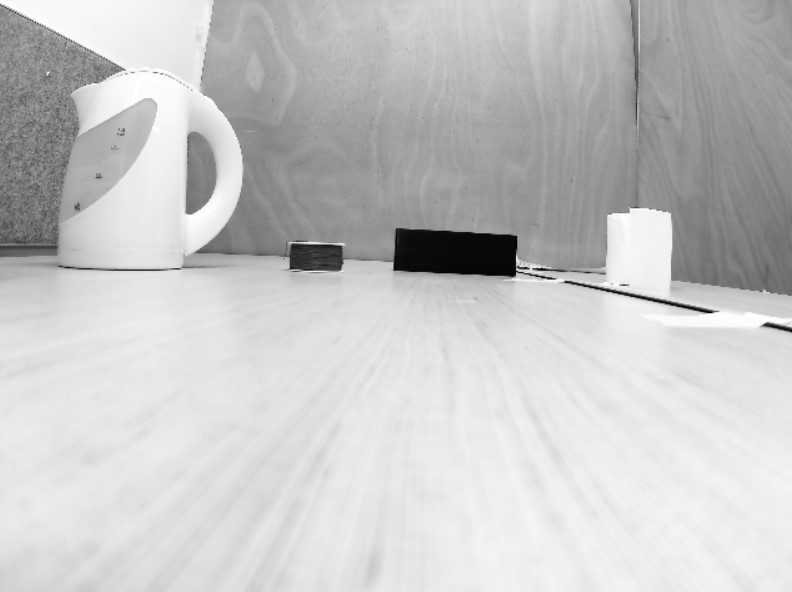
yolo/images/img9.jpg
