ShakedDanZilberman/Magdad/photographic_resources/opencv_test_frames/opencv_frame_4.png

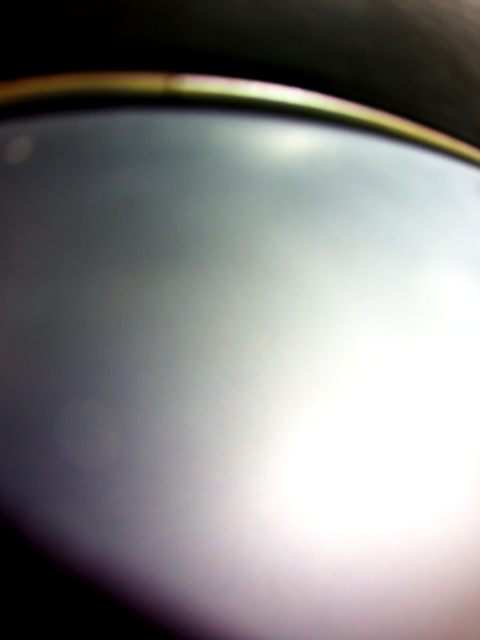
photographic_resources/opencv_test_frames/opencv_frame_4.png
