ShakedDanZilberman/Magdad/system/main.py

import time
import threading

import cv2
import numpy as np
from pyfirmata import Arduino, util
import matplotlib.pyplot as plt
# from ultralytics import YOLO

from contours import ContoursHandler
from changes import ChangesHandler
from cameraIO import detectCameras
from image_processing import RawHandler, ImageParse
from mouseCamera import MouseCameraHandler
from object_finder import show_targets, get_targets
from motion import DifferenceHandler
# from yolo import YOLOHandler
# from Trash.laser import LaserPointer
from cameraIO import Camera
from object_finder import average_of_heatmaps
# from Trash.gui import LIDARDistancesGraph
from gun import Gun, DummyGun
from constants import CAMERA_INDEX_0, CAMERA_INDEX_1, CAMERA_INDEX_2
from object_finder import Targets #GlobalTargets
# import homogrpahy
from constants import IMG_WIDTH, IMG_HEIGHT, homography_matrix, homography_matrices

timestep = 0  # Global timestep, used to keep track of the number of frames processed
laser_targets = [(30, 60)]  # List of targets for the laser pointer, used to share information between threads
gun_targets = []  # List of targets for the gun, used to share information between threads
P_ERROR = -75
I_ERROR = -25
D_ERROR = 0
total_error = 0
last_error = 0
error = 0
fix = 0
DIFF_THRESH = 0
INITIAL_CONTOUR_EXTRACT_FRAME_NUM = 30
CHECK_FOR_NEW_OBJECTS = 48




def shoot(target):
    print("Shooting", target)


def laser_thread():
    """
    Thread that moves the laser pointer to the target.
    The targets are aquired as an asynchronous input from the main thread.
    Only this thread may access LaserPointer which controls the laser pointer and the LIDAR.
    """
    print("Laser thread started.")
    global laser_targets, laser_point
    laser_pointer = LaserPointer()
    print("Laser pointer initialised and connected.")
    distances_interative_graph = LIDARDistancesGraph(show=False)
    while True:
        my_targets = laser_targets.copy()
        my_targets = sorted(my_targets, key=lambda x: x[0])  # sort by x coordinate to create a smooth left-to-right movement
        for center in my_targets:
            # Move the laser pointer to the target
            laser_pointer.move(center)

            # Measure the distance to the target
            distance = laser_pointer.distance()
            distances_interative_graph.add_distance(distance)
            print("Measured distance:", distances_interative_graph.distance())
            distances_interative_graph.plot()

            time.sleep(0.1)
        time.sleep(0.1)

    plt.ioff()
    plt.show()


def hit_cursor_main():
    """
    An alternative to the main function that uses the mouse cursor as the target for the laser pointer.
    It does not use any image processing to detect targets.
    """
    global CAMERA_INDEX_0, timestep, laser_targets
    import Trash.fit as fit
    detectCameras()
    cam = Camera(CAMERA_INDEX_0)
    handler = MouseCameraHandler()
    # laser = threading.Thread(target=laser_thread)
    # laser.start()  # comment this line to disable the laser pointer
    gun = Gun()  # DummyGun() or Gun()

    cv2.namedWindow(handler.TITLE)
    cv2.setMouseCallback(handler.TITLE, handler.mouse_callback)
    thetaX = 90.00
    while True:
        img = cam.read()

        handler.add(img)
        handler.display()

        mousePos = handler.getMousePosition()
        laser_targets = [mousePos]
        last_thetaX = thetaX
        thetaX, expected_volt = fit.bilerp(*mousePos)
        
        # # use PID
        # global fix
        # if thetaX != last_thetaX:
        #     gun.rotate(thetaX)
        #     global last_error, total_error
        #     last_error = 0 
        #     total_error = 0
        #     time.sleep(0.5)
        # else:
        #     gun.rotate(thetaX + fix)
        # motor_volt = gun.get_voltage()
        # fix = PID(expected_volt,motor_volt) 
        
        
        if cv2.waitKey(1) == 32:  # Whitespace
            gun.shoot()
        # Press Escape to exit
        if cv2.waitKey(1) == 27:
            break
    cv2.destroyAllWindows()





def PID (expected_volt, motor_volt):
    # use PID      
        global total_error, last_error, error
        last_error = error
        if motor_volt is None or expected_volt is None:
            error = 0
        else:
            error = motor_volt - expected_volt
        dif_error = error - last_error
        total_error += error
        print("Motor voltage:", motor_volt, "Expected voltage:", expected_volt, "Error:", error)
        return error*P_ERROR + total_error*I_ERROR + dif_error*D_ERROR


def just_changes_main():
    """
    This function uses the changes in the image to detect targets.
    It does not use contours or YOLO.
    It is a simplified version of the main function.
    """
    global CAMERA_INDEX_0, timestep, gun_targets
    detectCameras()
    cam = Camera(CAMERA_INDEX_0)
    rawHandler = RawHandler("Whitespace to clear")
    changesHandler = ChangesHandler()

    def gun_thread():
        """
        Thread that moves the gun to the target and shoots.
        The targets are aquired as an asynchronous input from the main thread.
        """
        import Trash.fit as fit
        print("Gun thread started.")
        global gun_targets
        gun = Gun()
        print("Gun initialised and connected.")
        while True:
            my_targets = gun_targets.copy()
            # Sort by x coordinate to create a smooth right-to-left movement
            my_targets = sorted(my_targets, key=lambda x: x[0], reverse=True)
            for center in my_targets:
                # Move the laser pointer to the target
                thetaX, expected_volt = fit.bilerp(*center)
                # use PID
                motor_volt = gun.get_voltage()
                error = PID(expected_volt,motor_volt)  
                gun.rotate(thetaX + error)
                print("Shooting", center)
            time.sleep(1)
        # TODO: It seems gun_thread is not moving, even though the targets are being updated. FIX

    
    gun = threading.Thread(target=gun_thread)
    gun.start()
    
    while True:
        timestep += 1
        img = cam.read()

        rawHandler.add(img)
        rawHandler.display()
        
        changesHandler.add(img)
        changesHandler.display()

        img_changes = changesHandler.get()

        FRAME_TITLE = "Targets from Changes"

        if isinstance(img_changes, np.ndarray) and img_changes.size > 1:
            targets_changes = circles_high, circles_low, centers_changes = get_targets(img_changes)
            show_targets(FRAME_TITLE, img_changes, targets_changes)
        else:
            targets_changes = circles_high, circles_low, centers_changes = [], [], []
            show_targets(FRAME_TITLE, img_changes, targets_changes)

        # add the targets from the changes to the queue
        if len(centers_changes) > 0:
            # Remove from centers_changes any targets that are less than 30 pixels apart (unique targets)
            targets = []
            pixel_distance = 30
            for center in centers_changes:
                if all(np.linalg.norm(np.array(center) - np.array(target)) > pixel_distance for target in targets):
                    targets.append(center)
            gun_targets = targets.copy()
            print("Targets:", gun_targets)
        
        if cv2.waitKey(1) == 32:  # Whitespace
            changesHandler.clear()

        # Press Escape to exit
        if cv2.waitKey(1) == 27:
            break
    cv2.destroyAllWindows()


def main():
    global CAMERA_INDEX_0, timestep, laser_targets
    detectCameras()
    cam = Camera(CAMERA_INDEX_0)
    rawHandler = RawHandler()
    changesHandler = ChangesHandler()
    differenceHandler = DifferenceHandler()
    contoursHandler = ContoursHandler()
    yoloHandler = YOLOHandler()
    laser = threading.Thread(target=laser_thread)
    laser.start()
    target_queue = []
    target = None
    
    while True:
        timestep += 1
        img = cam.read()

        for handler in [
            rawHandler,
            changesHandler,
            differenceHandler,
            contoursHandler,
            yoloHandler,
        ]:
            handler.add(img)
            handler.display()
        # rawHandler.display()
        # changesHandler.display()
        img_contours = contoursHandler.get()
        img_changes = changesHandler.get()
        img_objects = yoloHandler.get()  # TODO: Use the bounding boxes to get the targets
        # TODO: make the decision algorithm more robust, clear, and DRY
        # get the targets using the contour detection method
        circles_high, circles_low, centers_contours = get_targets(img_contours)
        targets_contours = circles_high, circles_low, centers_contours
        # show them on screen
        circles_high, circles_low, centers_changes = show_targets("img_contours", img_contours, targets_contours)

        if isinstance(img_changes, np.ndarray) and img_changes.size > 1:
            # get the targets using the image diffrecnce method
            circles_high, circles_low, centers_changes = get_targets(img_changes)
            targets_changes = circles_high, circles_low, centers_changes
            # show them on screen
            circles_high, circles_low, centers_changes = show_targets("img_changes", img_changes, targets_changes)
        else:
            circles_high, circles_low, centers_changes = [], [], []
            targets_changes = circles_high, circles_low, centers_changes
        # extract the objects using contour detection
        if timestep == INITIAL_CONTOUR_EXTRACT_FRAME_NUM:
            for center in centers_contours:
                target_queue.append(center)
                laser_targets.append(center)
        # at a constant rate, check for changes between the current image and and the original image
        elif timestep%CHECK_FOR_NEW_OBJECTS == CHECK_FOR_NEW_OBJECTS-1 and ImageParse.image_sum(differenceHandler.get()) is not None and ImageParse.image_sum(differenceHandler.get()) <= DIFF_THRESH:
                # add all new objects in the image 
                for center in centers_changes:
                    laser_targets.append(center)
                    target_queue.append(center)
                # immediately after adding targets to the target queue, reset the image changes heatmap, 
                # so that the movements of objects caused by shooting do not count as new targets
                changesHandler.clear()
                # get the changes image again
                img_changes = changesHandler.get()
        # print("queue:", centers)
        if timestep % CHECK_FOR_NEW_OBJECTS == 0 and len(target_queue) > 0:
            target = target_queue.pop(0)
            
            if not target == None:
                laser_targets.append(target)
                target = None
        
        if cv2.waitKey(1) == 32:  # Whitespace
            changesHandler.clear()

        # Press Escape to exit
        if cv2.waitKey(1) == 27:
            break
    cv2.destroyAllWindows()


def main_using_targets():
    global CAMERA_INDEX_0, timestep, gun_targets
    from Trash.gui import GUI
    detectCameras()
    cam = Camera(CAMERA_INDEX_0)
    rawHandler = RawHandler()
    target_manager = Targets()
    gui = GUI()
    def gun_thread():
        """
        Thread that moves the gun to the target and shoots.
        The targets are aquired as an asynchronous input from the main thread.
        """
        import Trash.fit as fit
        print("Gun thread started.")
        global gun_targets
        gun = Gun(print_flag=True)
        center = (IMG_WIDTH//2, IMG_HEIGHT//2)
        while True:
            # TODO: test out pop_closest_to_current_location as an alternative to pop() 
            # center, to_shoot = target_manager.pop_closest_to_current_location(center)
            center = target_manager.pop()
            # Move the laser pointer to the target
            to_shoot = center is not None
            if to_shoot:
                gun.aim_and_fire_target_2(center)
                print("Shooting (theoretically)", center)
                time.sleep(1) # this delay is here so we can wait for the objects to fall and then reset the changes image
                target_manager.clear() # TODO: reduce the number of frames needed for initialization
    
    gun = threading.Thread(target=gun_thread)
    gun.start()
    
    while True:
        timestep += 1
        # the following if is to reduce the FPS to 10:
        img = cam.read()
        to_check = timestep % 15 == 7
        to_init = timestep == 5
        rawHandler.add(img)
        rawHandler.display()
        target_manager.add(img, to_check)
        # Press Escape to exit
        if cv2.waitKey(1) == 27:
            break
    cv2.destroyAllWindows()


def main_using_targets_and_homography():
    global CAMERA_INDEX_0, timestep, gun_targets
    from Trash.gui import GUI
    detectCameras()
    cam = Camera(CAMERA_INDEX_0)
    rawHandler = RawHandler()
    target_manager = Targets()
    gui = GUI()
    def gun_thread():
        """
        Thread that moves the gun to the target and shoots.
        The targets are aquired as an asynchronous input from the main thread.
        """
        import Trash.fit as fit
        print("Gun thread started.")
        global gun_targets
        gun = Gun(print_flag=True)
        center = (IMG_WIDTH//2, IMG_HEIGHT//2)
        while True:
            # TODO: test out pop_closest_to_current_location as an alternative to pop() 
            center = target_manager.pop_closest_to_current_location(center)
            # Move the laser pointer to the target
            if center is not None:
                aim_and_fire(gun,center)
                aim_and_fire(gun,center)
                print("Shooting (theoretically)", center)
                time.sleep(1) # this delay is here so we can wait for the objects to fall and then reset the changes image
                target_manager.clear() # TODO: reduce the number of frames needed for initialization
    
    def aim_and_fire(gun,center_pixels):
        import math
        gun_real_pos = (0,0)
        real_world_pos = cv2.perspectiveTransform(center_pixels, homography_matrix)
        theta = math.arctan((real_world_pos[0]-gun_real_pos[0])/(real_world_pos[1]-gun_real_pos[1]))*180/math.pi
        gun.rotate(theta)
        time.sleep(0.2)
        gun.shoot
        
    
    def aim_and_fire(gun,center_pixels):
        import math
        gun_real_pos = (0,0)
        real_world_pos = cv2.perspectiveTransform(center_pixels, homography_matrix)
        theta = math.arctan((real_world_pos[0]-gun_real_pos[0])/(real_world_pos[1]-gun_real_pos[1]))*180/math.pi
        gun.rotate(theta)
        time.sleep(0.2)
        gun.shoot
        
    
    gun = threading.Thread(target=gun_thread)
    gun.start()
    
    while True:
        timestep += 1
        img = cam.read()
        rawHandler.add(img)
        rawHandler.display()
        target_manager.add(timestep, img)
        # Press Escape to exit
        if cv2.waitKey(1) == 27:
            break
    cv2.destroyAllWindows()



def main_using_targets_3_cameras():
    global CAMERA_INDEX_0, timestep, gun_targets
    from Trash.gui import GUI
    detectCameras()
    cam = Camera(CAMERA_INDEX_0)
    rawHandler = RawHandler()
    target_manager1 = Targets()
    target_manager2 = Targets()
    target_manager3 = Targets()
    global_target_manager = GlobalTargets(target_manager1, target_manager2, target_manager3)
    gui = GUI()
    def gun_thread():
        """
        Thread that moves the gun to the target and shoots.
        The targets are aquired as an asynchronous input from the main thread.
        """
        import Trash.fit as fit
        print("Gun thread started.")
        global gun_targets
        gun = Gun(print_flag=True)
        center = (IMG_WIDTH//2, IMG_HEIGHT//2)
        while True:
            # TODO: (ayala) write the function pop_closest_to_current_location or regular pop, in the GlobalTargets class
            # TODO: test out pop_closest_to_current_location as an alternative to pop()
            center = global_target_manager.pop_closest_to_current_location(center)
            # Move the laser pointer to the target
            if center is not None:
                gun.aim_and_fire_target_2(center)
                print("Shooting (theoretically)", center)
                time.sleep(1) # this delay is here so we can wait for the objects to fall and then reset the changes image
                target_manager1.clear() # TODO: reduce the number of frames needed for initialization
    
    gun = threading.Thread(target=gun_thread)
    gun.start()
    
    while True:
        timestep += 1
        img = cam.read()
        rawHandler.add(img)
        rawHandler.display()
        target_manager1.add(timestep, img)
        # Press Escape to exit
        if cv2.waitKey(1) == 27:
            break
    cv2.destroyAllWindows()


def test_main():
    global CAMERA_INDEX_0, timestep, gun_targets
    detectCameras()
    cam = Camera(CAMERA_INDEX_0)
    rawHandler = RawHandler()
    contours_handler = ChangesHandler()

    while True:
        timestep += 1
        img = cam.read()
        rawHandler.add(img)
        rawHandler.display()
        contours_handler.add(img)
        contours_handler.display()
        img_contours = contours_handler.get()
        targets_contours = _, _, contours_centers = get_targets(img_contours)
        # show_targets("targets from contours", img_contours, targets_contours)
        
        if cv2.waitKey(1) == 27:
            break
    cv2.destroyAllWindows()


def test():
    gun = Gun(print_flag=True)
    while True:
        gun.rotate(60)
        print(gun.get_voltage()) 
        gun.shoot()
        time.sleep(1)
    print("done")





def test_camera():
    global CAMERA_INDEX_0, timestep
    detectCameras()
    cam = Camera(CAMERA_INDEX_0)
    handler = RawHandler()
    # laser = threading.Thread(target=laser_thread)
    # laser.start()  # comment this line to disable the laser pointer

    # cv2.namedWindow(handler.TITLE)
    frame_num = 0
    while True:
        img = cam.read(frame_num)
        # cv2.imshow("raw image", img)
        handler.add(img)
        handler.display()
        frame_num+=1

        # Press Escape to exit
        if cv2.waitKey(1) == 27:
            # print(real_world_pos)
            break
    cv2.destroyAllWindows()


def main_using_targets():
    global CAMERA_INDEX_0, timestep, gun_targets
    from Trash.gui import GUI
    detectCameras()
    cam = Camera(CAMERA_INDEX_0)
    rawHandler = RawHandler()
    target_manager = Targets()
    gui = GUI()
    def gun_thread():
        """
        Thread that moves the gun to the target and shoots.
        The targets are aquired as an asynchronous input from the main thread.
        """
        import Trash.fit as fit
        print("Gun thread started.")
        global gun_targets
        gun = Gun(print_flag=True)
        center = (IMG_WIDTH//2, IMG_HEIGHT//2)
        while True:
            # TODO: test out pop_closest_to_current_location as an alternative to pop() 
            center = target_manager.pop_closest_to_current_location(center)
            # Move the laser pointer to the target
            if center is not None:
                gun.aim_and_fire_target_2(center)
                print("Shooting (theoretically)", center)
                time.sleep(1) # this delay is here so we can wait for the objects to fall and then reset the changes image
                target_manager.clear() # TODO: reduce the number of frames needed for initialization
    
    gun = threading.Thread(target=gun_thread)
    gun.start()
    
    while True:
        timestep += 1
        img = cam.read()
        rawHandler.add(img)
        rawHandler.display()
        target_manager.add(timestep, img)
        # Press Escape to exit
        if cv2.waitKey(1) == 27:
            break
    cv2.destroyAllWindows()

def hit_cursor_main_2():
    """
    An alternative to the main function that uses the mouse cursor as the target for the laser pointer.
    It does not use any image processing to detect targets.
    """
    global CAMERA_INDEX_0, timestep, laser_targets
    import Trash.fit as fit
    detectCameras()
    cam = Camera(CAMERA_INDEX_0)
    handler = MouseCameraHandler()
    # laser = threading.Thread(target=laser_thread)
    # laser.start()  # comment this line to disable the laser pointer
    gun = Gun()  # DummyGun() or Gun()

    cv2.namedWindow(handler.TITLE)
    cv2.setMouseCallback(handler.TITLE, handler.mouse_callback)
    thetaX = 90.00
    while True:
        img = cam.read()

        handler.add(img)
        handler.display()

        mousePos = handler.getMousePosition()
        laser_targets = [mousePos]
        last_thetaX = thetaX
        thetaX, expected_volt = fit.bilerp(*mousePos)
        # use PID
        global fix
        if thetaX != last_thetaX:
            gun.rotate(thetaX)
            global last_error, total_error
            last_error = 0 
            total_error = 0
            time.sleep(0.5)
        else:
            gun.rotate(thetaX + fix)
        motor_volt = gun.get_voltage()
        fix = PID(expected_volt,motor_volt) 
        
        
        if cv2.waitKey(1) == 32:  # Whitespace
            gun.shoot()
        # Press Escape to exit
        if cv2.waitKey(1) == 27:
            break
    cv2.destroyAllWindows() 
    
def homography_targets():
    global CAMERA_INDEX_0, timestep, gun_targets
    from Trash.gui import GUI
    detectCameras()
    cam = Camera(CAMERA_INDEX_0)
    rawHandler = RawHandler()
    target_manager = Targets()
    frame_num = 0
    while True:
        timestep += 1
        img = cam.read(frame_num)
        rawHandler.add(img)
        rawHandler.display()
        target_manager.add(timestep, img)
        # Press Escape to exit
        center = target_manager.pop_closest_to_current_location(center)
        real_world_pos = cv2.perspectiveTransform(center, homography_matrix)
        print("real world")
        print(real_world_pos)
        frame_num+=1
        
        if cv2.waitKey(1) == 27:
            break
    cv2.destroyAllWindows()

def homography_calibration_main():
    """
    An alternative to the main function that uses the mouse cursor as the target for the laser pointer.
    It does not use any image processing to detect targets.
    """
    global CAMERA_INDEX_2, timestep, laser_targets
    detectCameras()
    cam = Camera(CAMERA_INDEX_2)
    handler = MouseCameraHandler(CAMERA_INDEX_2)
    # laser = threading.Thread(target=laser_thread)
    # laser.start()  # comment this line to disable the laser pointer

    cv2.namedWindow("camera " + str(CAMERA_INDEX_2) + " view")
    cv2.setMouseCallback("camera " + str(CAMERA_INDEX_2) + " view", handler.mouse_callback)
    source_points = []
    frame_num = 0
    while True:
        img = cam.read()

        handler.add(img)
        handler.display(CAMERA_INDEX_2)
        if handler.has_new_clicks(): 
            click_pos = handler.get_clicks()
            print(click_pos)
            source_points.append([float(click_pos[0][0]), float(click_pos[0][1])])
            
        frame_num+=1
        # Press Escape to exit
        if cv2.waitKey(1) == 27:
            print(source_points)
            break
    cv2.destroyAllWindows()


def test_homography():
    global CAMERA_INDEX_0, timestep, laser_targets
    # import Trash.fit as fit
    # detectCameras()
    cam = Camera(CAMERA_INDEX_0)
    handler = MouseCameraHandler(CAMERA_INDEX_0)
    # laser = threading.Thread(target=laser_thread)
    # laser.start()  # comment this line to disable the laser pointer

    cv2.namedWindow(handler.title)
    cv2.setMouseCallback(handler.title, handler.mouse_callback)
    source_points = []
    frame_num = 0
    while True:
        img = cam.read()

        handler.add(img)
        handler.display()
        if handler.has_new_clicks(): 
            click_pos = handler.get_clicks()[0]
            click_pos_array = np.array([[[click_pos[0], click_pos[1]]]], dtype=np.float32)
            print("click is in pixel: ", click_pos)
            real_world_pos = cv2.perspectiveTransform(click_pos_array, homography_matrices[0])
            print(real_world_pos)
        frame_num+=1

        # Press Escape to exit
        if cv2.waitKey(1) == 27:
            # print(real_world_pos)
            break
    cv2.destroyAllWindows()


if __name__ == "__main__":
    # test()
    # hit_cursor_main()
    # just_changes_main()
    # main_using_targets_4()
    # homography_calibration_main()
    test_homography()
    # test_camera()
    # homography_targets()1
    
