ShakedDanZilberman/Magdad/Stepper/moves_forward_backward_6wire/moves_forward_backward_6wire.ino

// This code successfully moves a 6-wire stepper motor forward and backward.
// Choose the direction by changing the value of the dir variable in the doStep function in the loop.

#define RED 3 // Coil 1 - A
#define BLU 5 // Coil 1 - B
#define BLK 6 // Coil 2 - A'
#define GRN 4 // Coil 2 - B'

// #define pin1 6
// #define pin2 5
// #define pin3 4
// #define pin4 3

#define POSITIVE 1
#define NEGATIVE 0

#define DELAY_TIME 30 // Adjust to change speed

void setup()
{
    pinMode(LED_BUILTIN, OUTPUT);
    pinMode(RED, OUTPUT);
    pinMode(BLU, OUTPUT);
    pinMode(BLK, OUTPUT);
    pinMode(GRN, OUTPUT);

    digitalWrite(RED, LOW);
    digitalWrite(BLU, LOW);
    digitalWrite(BLK, LOW);
    digitalWrite(GRN, LOW);
}

void loop()
{
    doStep(NEGATIVE);
}

void doStep(int dir)
{
    stepMotorWrapper(0, dir);
    delay(DELAY_TIME);
    stepMotorWrapper(1, dir);
    delay(DELAY_TIME);
    stepMotorWrapper(2, dir);
    delay(DELAY_TIME);
    stepMotorWrapper(3, dir);
    delay(DELAY_TIME);
}

void stepMotorWrapper(int step, int dir)
{
    if (dir == POSITIVE)
    {
        stepMotor(step);
    }
    else
    {
        stepMotor(3 - step);
    }
}

void stepMotor(int step)
{
    switch (step)
    {
    case 0:
        digitalWrite(RED, HIGH);
        digitalWrite(BLU, LOW);
        digitalWrite(BLK, HIGH);
        digitalWrite(GRN, LOW);
        break;
    case 1:
        digitalWrite(RED, LOW);
        digitalWrite(BLU, HIGH);
        digitalWrite(BLK, HIGH);
        digitalWrite(GRN, LOW);
        break;
    case 2:
        digitalWrite(RED, LOW);
        digitalWrite(BLU, HIGH);
        digitalWrite(BLK, LOW);
        digitalWrite(GRN, HIGH);
        break;
    case 3:
        digitalWrite(RED, HIGH);
        digitalWrite(BLU, LOW);
        digitalWrite(BLK, LOW);
        digitalWrite(GRN, HIGH);
        break;
    }
}
