ShakedDanZilberman/Magdad/Trash/test_camera.py

import cv2
from image_processing import ImageParse

# Open the default camera
cam = cv2.VideoCapture(0, cv2.CAP_MSMF)


cam.set(cv2.CAP_PROP_FRAME_WIDTH, 1920)
cam.set(cv2.CAP_PROP_FRAME_HEIGHT, 1080)
 

# Get the default frame width and height
frame_width = int(cam.get(cv2.CAP_PROP_FRAME_WIDTH))
frame_height = int(cam.get(cv2.CAP_PROP_FRAME_HEIGHT))
print(cam.get(cv2.CAP_PROP_FRAME_WIDTH), cam.get(cv2.CAP_PROP_FRAME_HEIGHT))

# Define the codec and create VideoWriter object
# fourcc = cv2.VideoWriter_fourcc(*'mp4v')
# out = cv2.VideoWriter('output.mp4', fourcc, 20.0, (frame_width, frame_height))

while True:
    ret, frame = cam.read()
    
    # Write the frame to the output file
    # out.write(frame)
    frame = ImageParse.resize_proportionally(frame, 0.5)
    # Display the captured frame
    cv2.imshow('Camera', frame)

    # Press 'q' to exit the loop
    if cv2.waitKey(1) == ord('q'):
        break

# Release the capture and writer objects
cam.release()
# out.release()
cv2.destroyAllWindows()
